WeirdConstructor/3DPrining_MakerGrid/res/containers.png

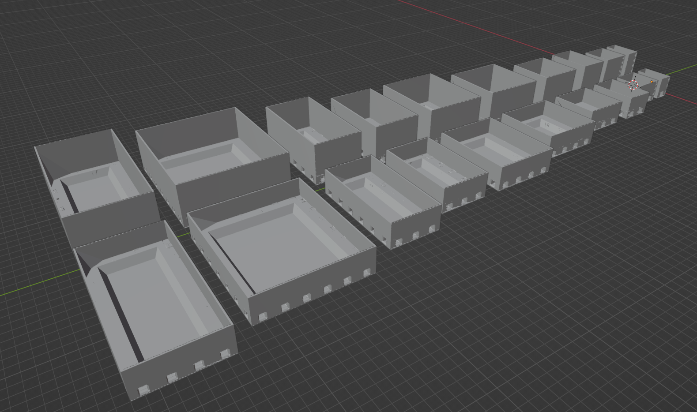
res/containers.png
