WeirdConstructor/3DPrining_MakerGrid/res/containers_demo.jpg

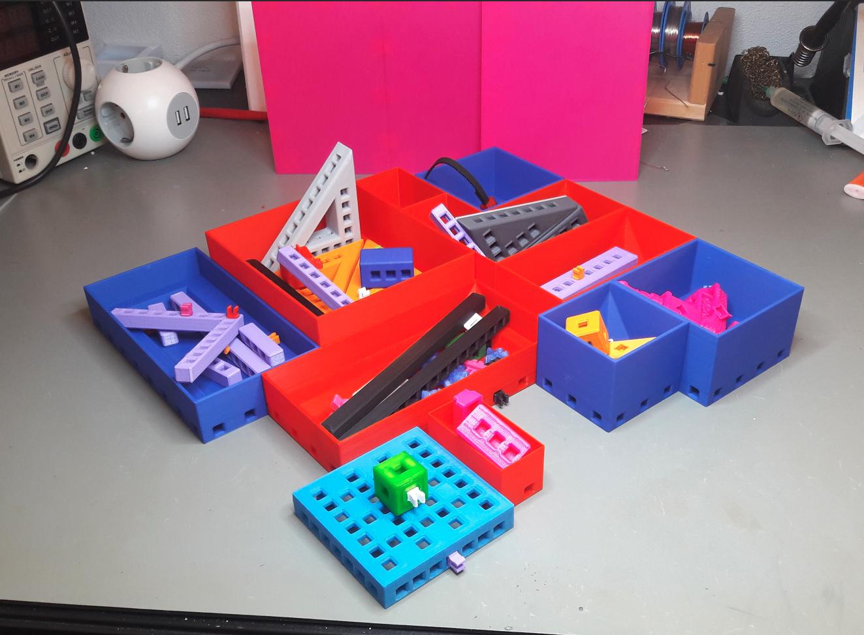
res/containers_demo.jpg
