WeirdConstructor/3DPrining_MakerGrid/res/fan_mount_50mm.jpg

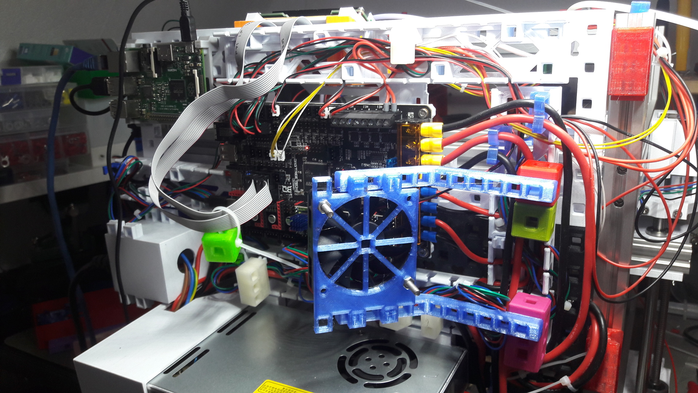
res/fan_mount_50mm.jpg
