WeirdConstructor/3DPrining_MakerGrid/res/fan_mount_120mm.jpg

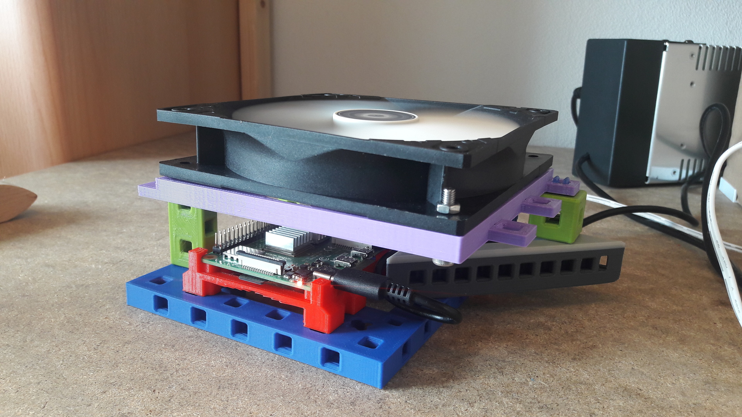
res/fan_mount_120mm.jpg
