WeirdConstructor/3DPrining_MakerGrid/res/m4_dovetail_mounts_demo.jpg

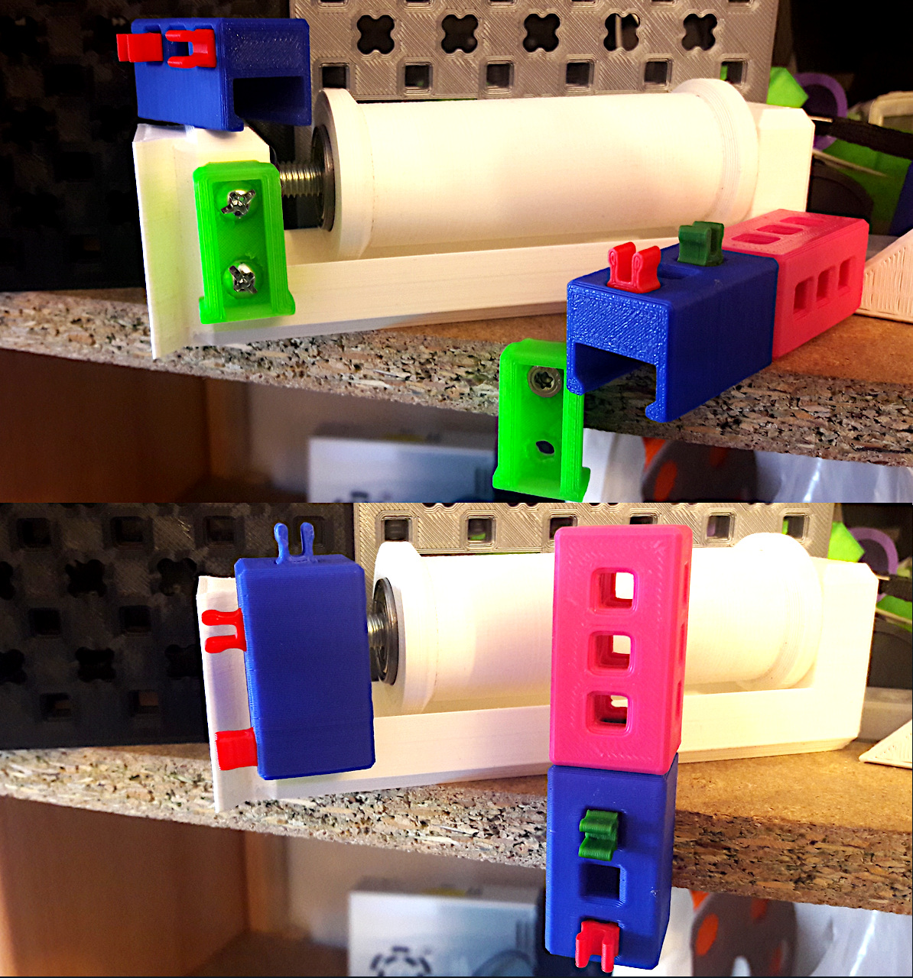
res/m4_dovetail_mounts_demo.jpg
