WeirdConstructor/3DPrining_MakerGrid/res/screwables_demo.jpg

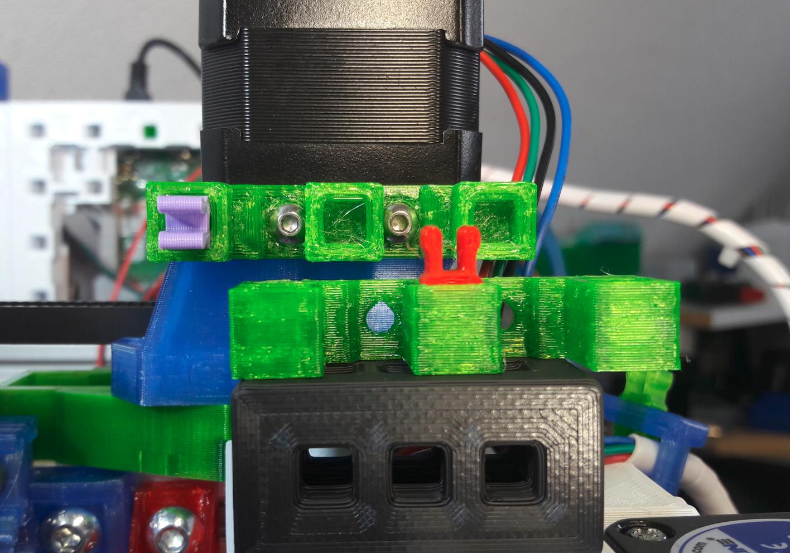
res/screwables_demo.jpg
