WeirdConstructor/3DPrining_MakerGrid/res/t_slot_20x20_nut6_mkg_clip_pic.jpg

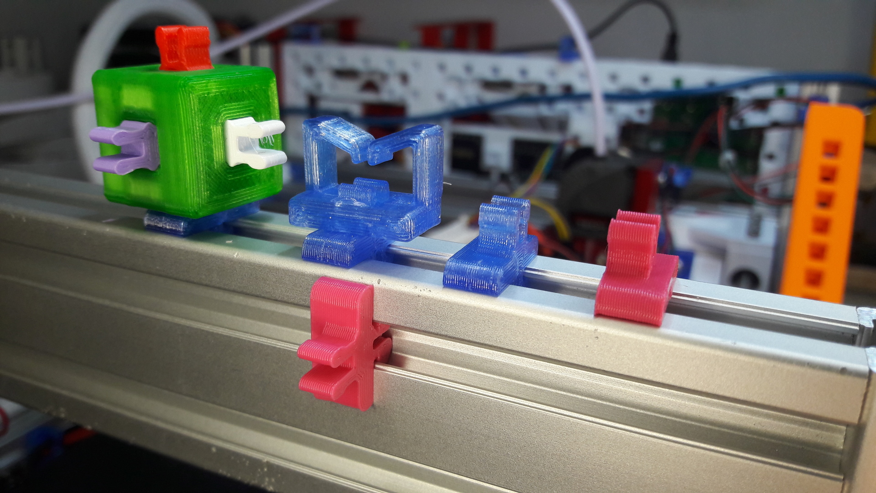
res/t_slot_20x20_nut6_mkg_clip_pic.jpg
