WeirdConstructor/3DPrining_MakerGrid/sliced/sliced_anycubic_i3_mega/clip_grid_2cm_type_b.3mf

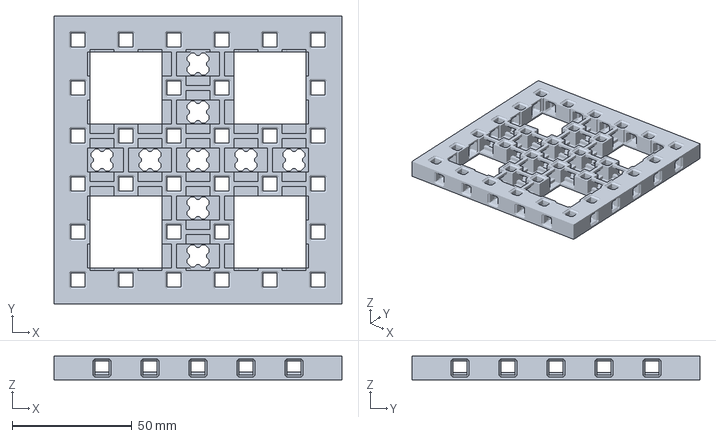
[picture p47: CAD file, 2022-01-15]
sliced/sliced_anycubic_i3_mega/clip_grid_2cm_type_b.3mf
120.0 x 120.0 x 10.0 mm
