WeirdConstructor/3DPrining_MakerGrid/sliced/sliced_kp3s/build_cubes-cube_side_con_11x1.3mf

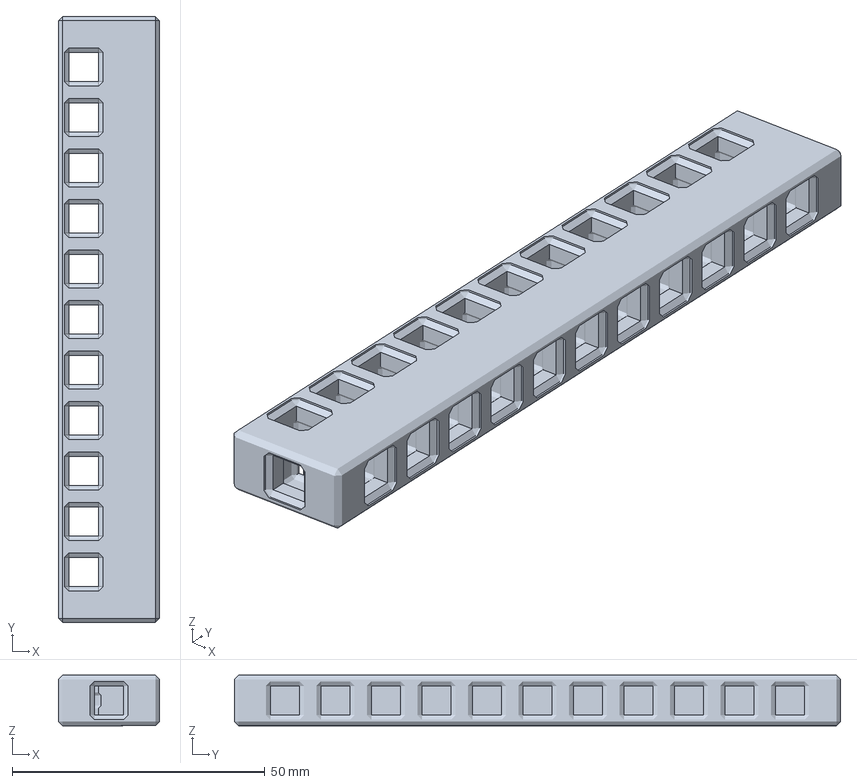
[picture p48: CAD file, 2022-01-27]
sliced/sliced_kp3s/build_cubes-cube_side_con_11x1.3mf
20.0 x 120.0 x 10.0 mm
