WeirdConstructor/3DPrining_MakerGrid/blender/cases/case_200x150x130-top_left.stl

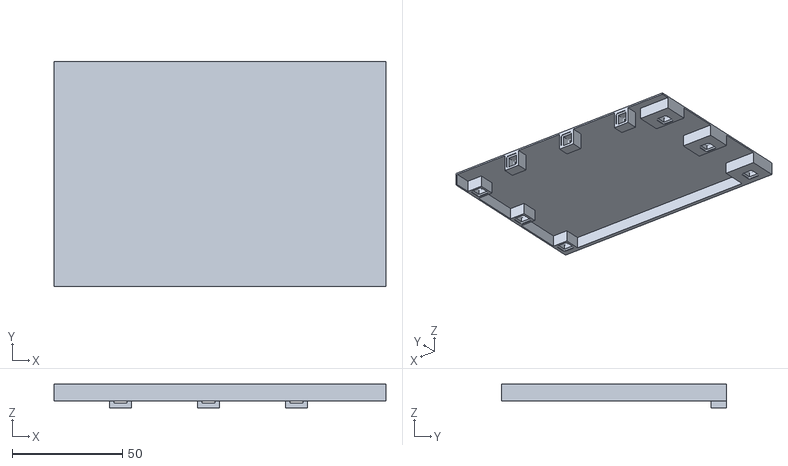
[picture p49: CAD file, 2024-06-11]
blender/cases/case_200x150x130-top_left.stl
150.9 x 102.4 x 10.7
