WeirdConstructor/3DPrining_MakerGrid/blender/clip_grid_2cm_case-cover_12x8.stl

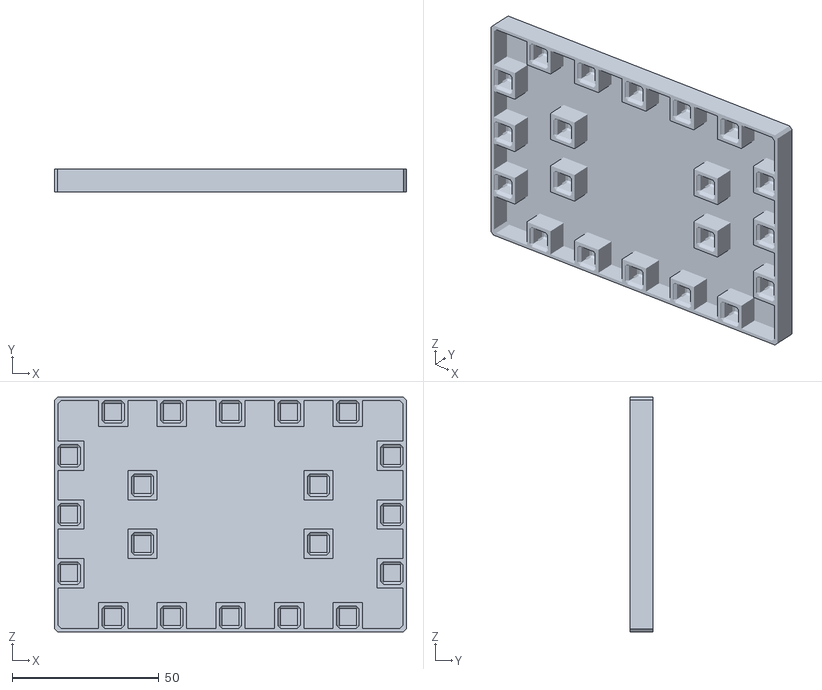
[picture p50: CAD file, 2024-04-21]
blender/clip_grid_2cm_case-cover_12x8.stl
120.0 x 7.89 x 80.0
