WeirdConstructor/3DPrining_MakerGrid/blender/devices/stepper_flag_Tight.stl

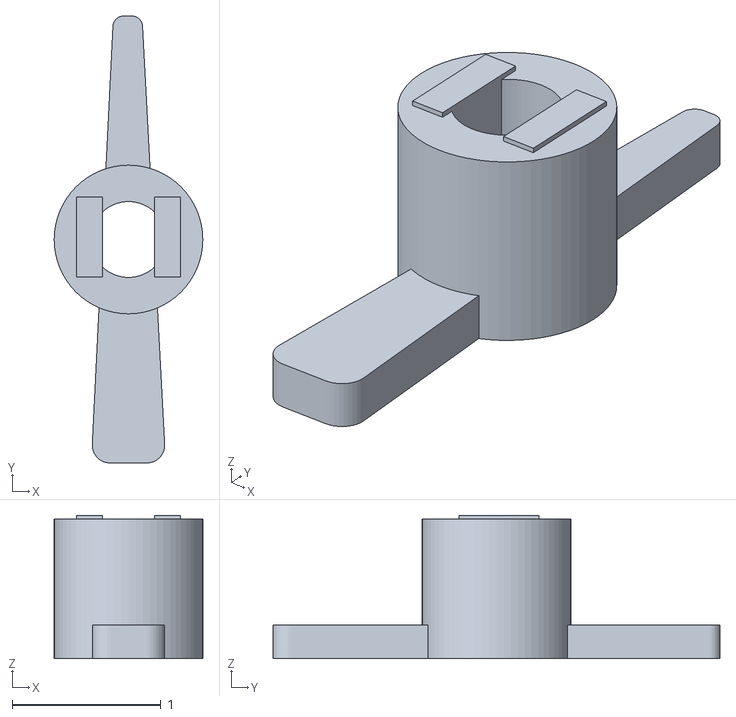
[picture p51: CAD file, 2024-04-28]
blender/devices/stepper_flag_Tight.stl
1.00 x 3.01 x 0.964
