WeirdConstructor/3DPrining_MakerGrid/blender/utils/hole_grid-hole_grid_pico.stl

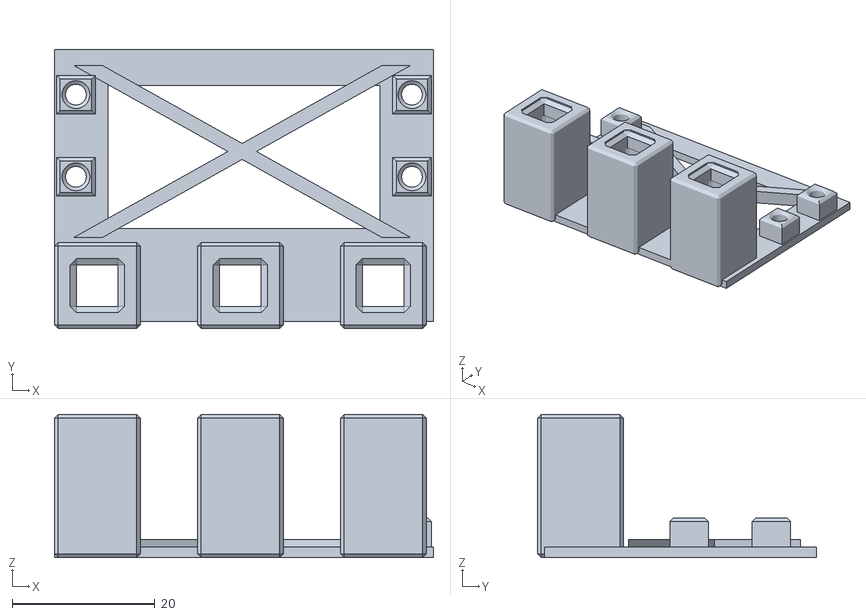
[picture p52: CAD file, 2024-06-11]
blender/utils/hole_grid-hole_grid_pico.stl
53.0 x 39.0 x 20.0
