WeirdConstructor/3DPrining_MakerGrid/sliced/sliced_anycubic_i3_mega/raspberry_pico_case_mkg_holder.3mf

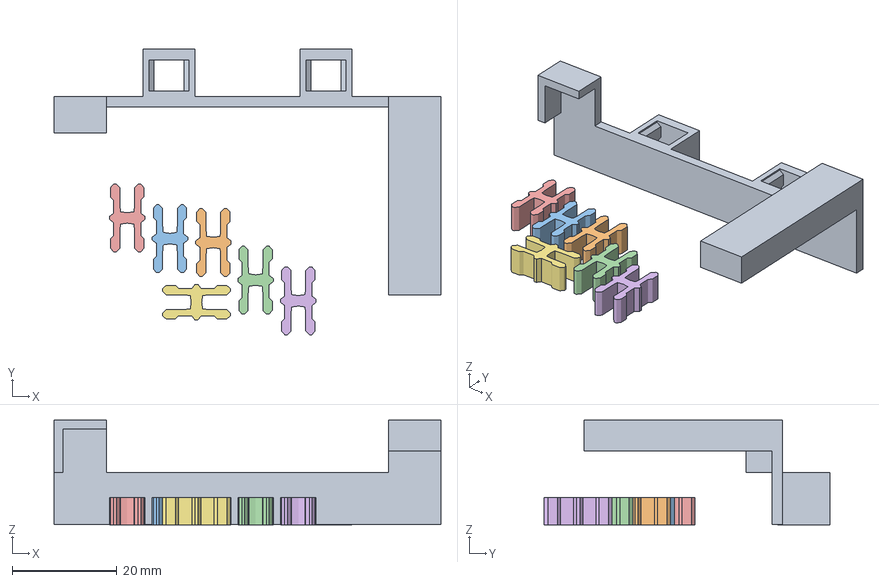
[picture p53: CAD file, 2022-01-14]
sliced/sliced_anycubic_i3_mega/raspberry_pico_case_mkg_holder.3mf
74.0 x 54.6 x 20.0 mm
raspberry_pico_case_mkg_holder.stl
clip.stl
clip.stl(1)
clip.stl(2)
clip.stl(3)
clip.stl(4)
clip.stl(5)
