WeirdConstructor/3DPrining_MakerGrid/sliced/sliced_kp3s/ptfe_tube-holder.3mf

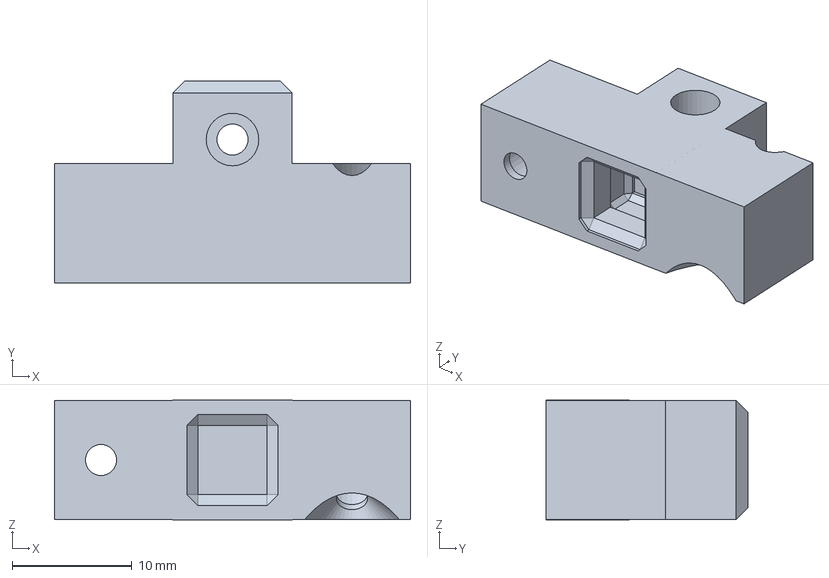
[picture p54: CAD file, 2022-01-24]
sliced/sliced_kp3s/ptfe_tube-holder.3mf
29.8 x 16.9 x 10.00 mm
