WeirdConstructor/3DPrining_MakerGrid/blender/Arduino-UNO.stl

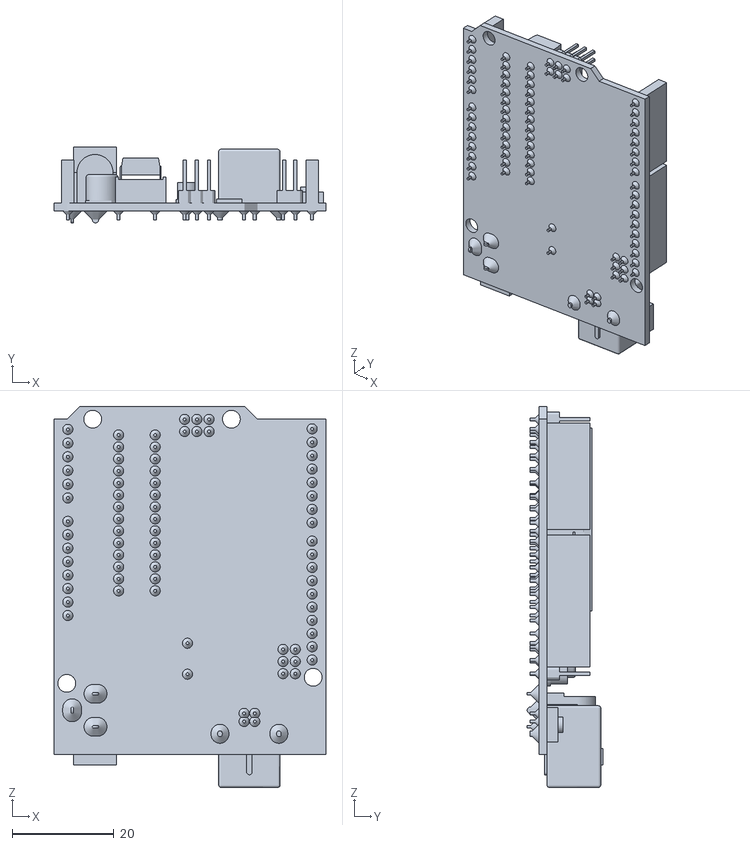
[picture p55: CAD file, 2024-03-30]
blender/Arduino-UNO.stl
53.5 x 14.9 x 75.0
