WeirdConstructor/3DPrining_MakerGrid/blender/devices/28byj-48_stepper_step_motor_holder-mkg_28byj_axis.stl

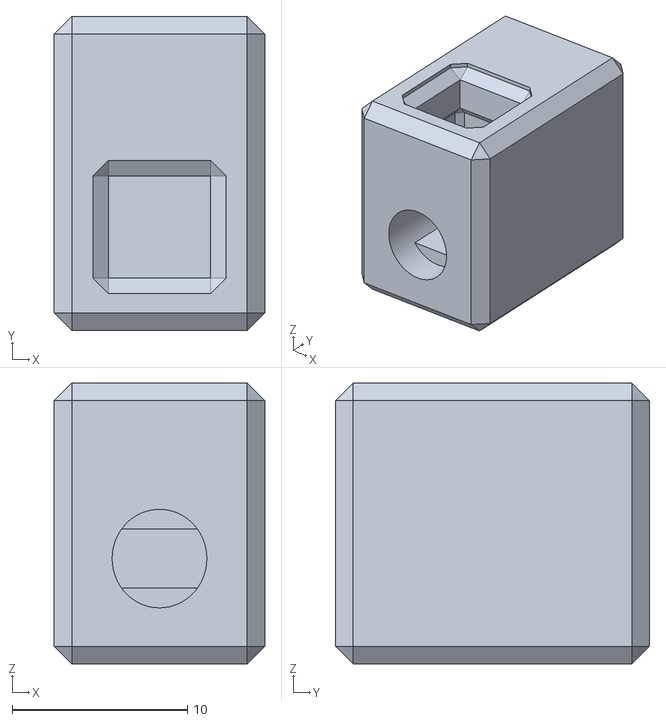
[picture p56: CAD file, 2024-04-28]
blender/devices/28byj-48_stepper_step_motor_holder-mkg_28byj_axis.stl
12.0 x 17.9 x 16.0
