WeirdConstructor/3DPrining_MakerGrid/blender/utils/plant_guide-hydro_wall_v2.stl

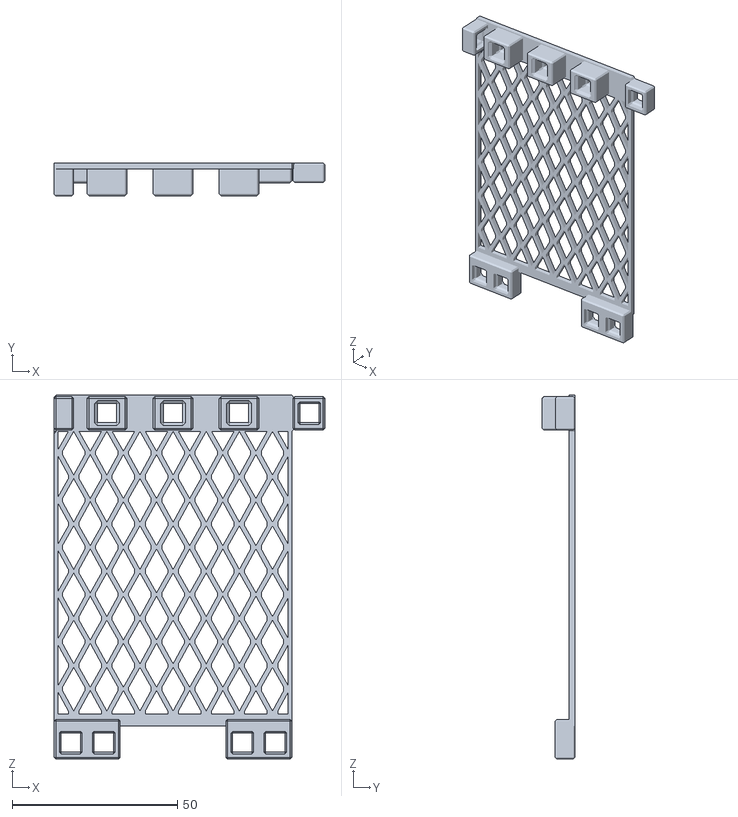
[picture p57: CAD file, 2024-06-11]
blender/utils/plant_guide-hydro_wall_v2.stl
82.0 x 10.0 x 110.3
