WeirdConstructor/3DPrining_MakerGrid/sliced/sliced_anycubic_i3_mega/cable_guide_a_v2.3mf

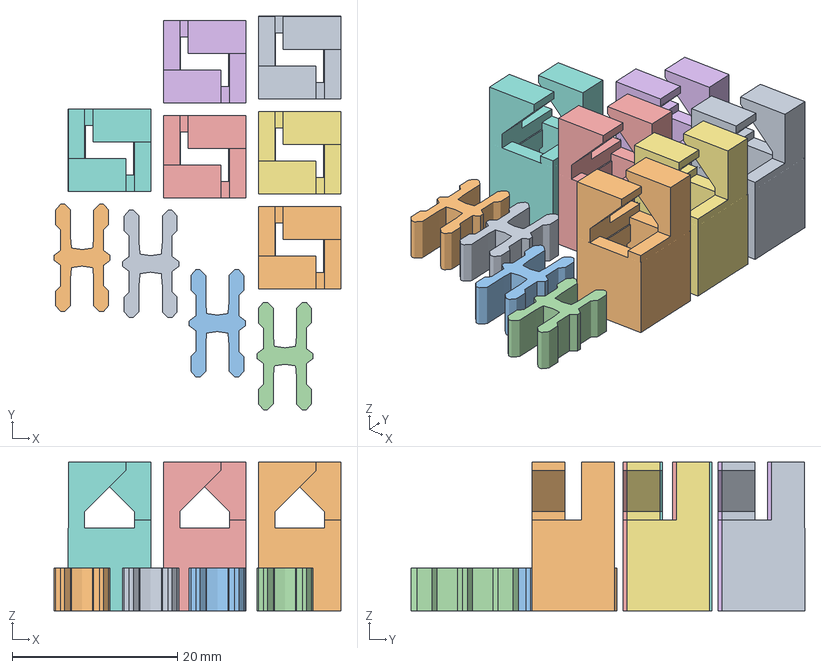
[picture p58: CAD file, 2022-01-14]
sliced/sliced_anycubic_i3_mega/cable_guide_a_v2.3mf
34.7 x 47.6 x 18.0 mm
clip.stl
clip.stl(1)
clip.stl(2)
clip.stl(4)
cable_guide_a_v2.stl
cable_guide_a_v2.stl(1)
cable_guide_a_v2.stl(2)
cable_guide_a_v2.stl(3)
cable_guide_a_v2.stl(4)
cable_guide_a_v2.stl(5)
