WeirdConstructor/3DPrining_MakerGrid/sliced/sliced_kp3s/glue_plate-plate_55x83.3mf

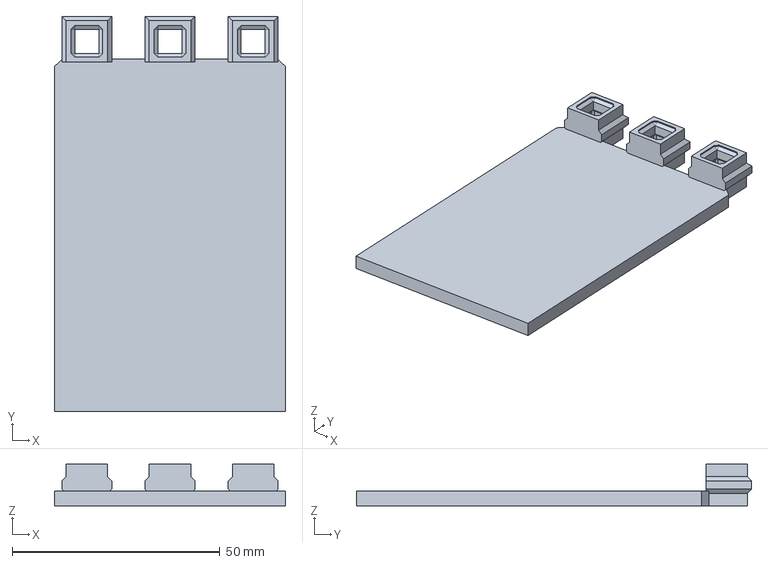
[picture p59: CAD file, 2022-01-24]
sliced/sliced_kp3s/glue_plate-plate_55x83.3mf
55.6 x 95.0 x 10.0 mm
