WeirdConstructor/3DPrining_MakerGrid/blender/cases/btt_octopus_plate-board_plate.stl

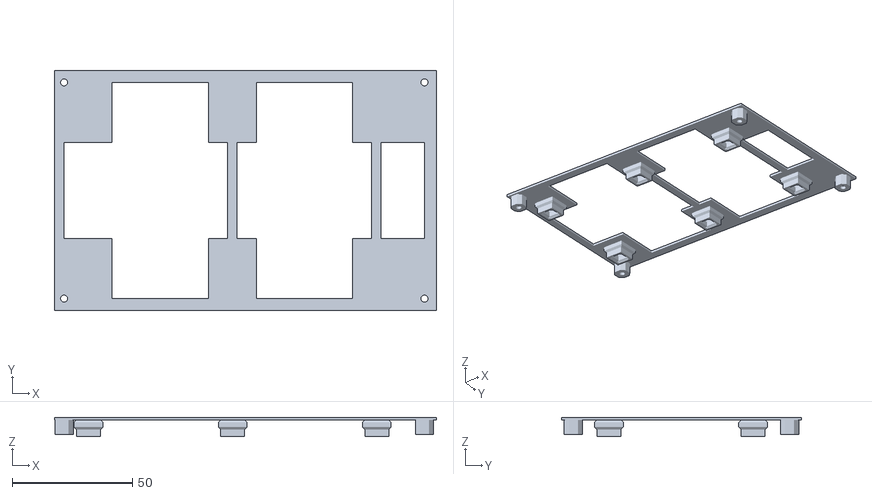
[picture p60: CAD file, 2022-03-17]
blender/cases/btt_octopus_plate-board_plate.stl
159.0 x 100.0 x 8.10
