WeirdConstructor/3DPrining_MakerGrid/blender/clip_grid_light_2cm-6x6.stl

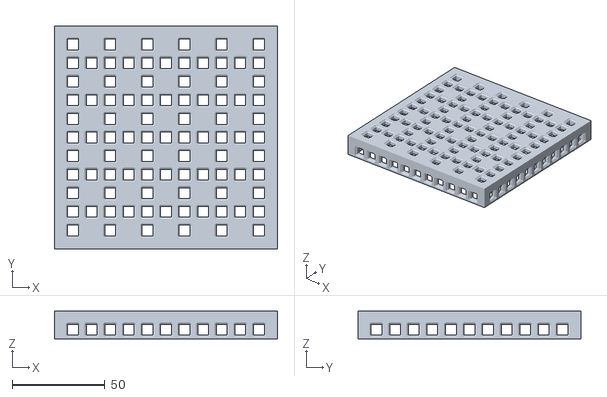
[picture p61: CAD file, 2022-06-01]
blender/clip_grid_light_2cm-6x6.stl
120.0 x 120.0 x 15.0
