WeirdConstructor/3DPrining_MakerGrid/blender/devices/Potentiometer.stl

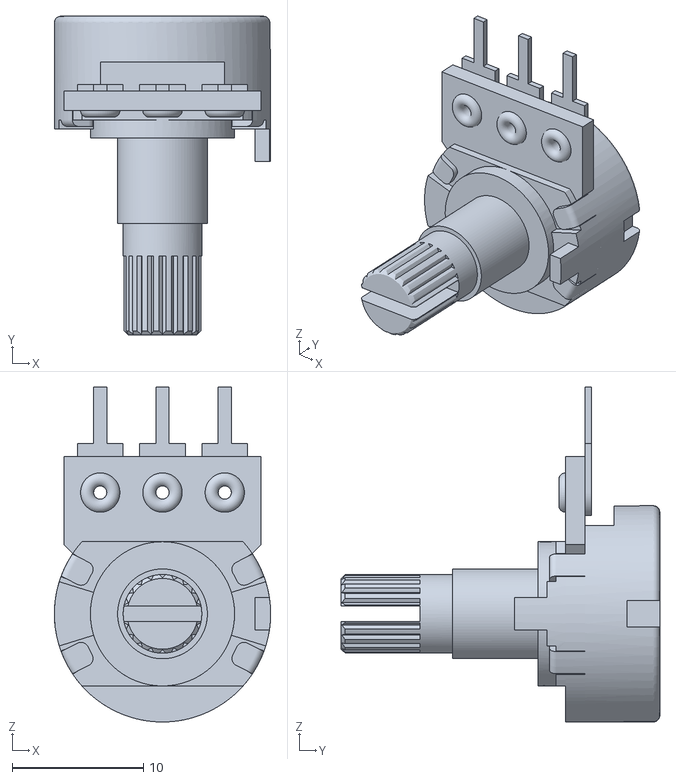
[picture p62: CAD file, 2024-04-28]
blender/devices/Potentiometer.stl
16.5 x 24.3 x 25.5
