WeirdConstructor/3DPrining_MakerGrid/blender/utils/hole_grid-gridcover_30x40.stl

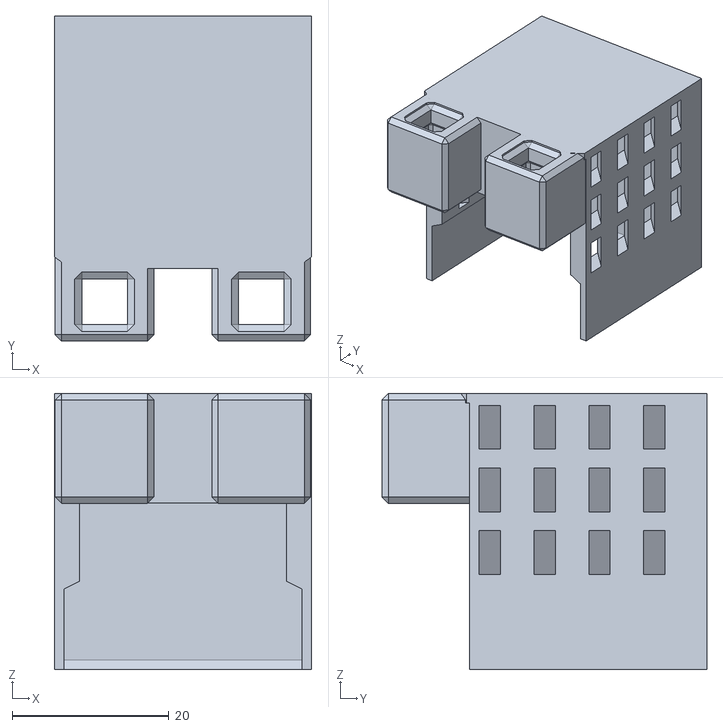
[picture p63: CAD file, 2024-06-11]
blender/utils/hole_grid-gridcover_30x40.stl
32.8 x 41.5 x 35.2
