WeirdConstructor/3DPrining_MakerGrid/sliced/sliced_kp3s/vise_holder-vise_4cm.3mf

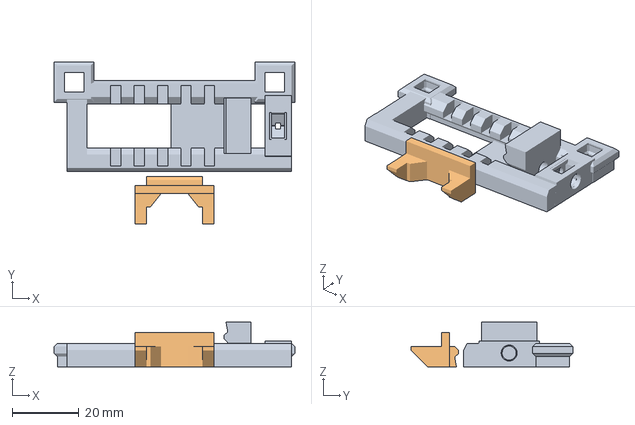
[picture p64: CAD file, 2022-01-20]
sliced/sliced_kp3s/vise_holder-vise_4cm.3mf
72.0 x 48.2 x 13.3 mm
vise_holder-vise_4cm.stl
vise_holder-vise_holder_insert.stl
