WeirdConstructor/3DPrining_MakerGrid/blender/cases/grid_case-wall_4x6.stl

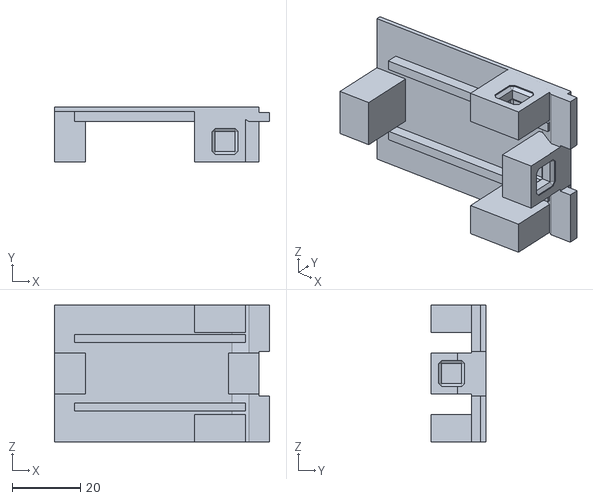
[picture p65: CAD file, 2022-02-05]
blender/cases/grid_case-wall_4x6.stl
62.9 x 16.0 x 40.0
