WeirdConstructor/3DPrining_MakerGrid/blender/clip_grid_light_2cm-2x2.stl

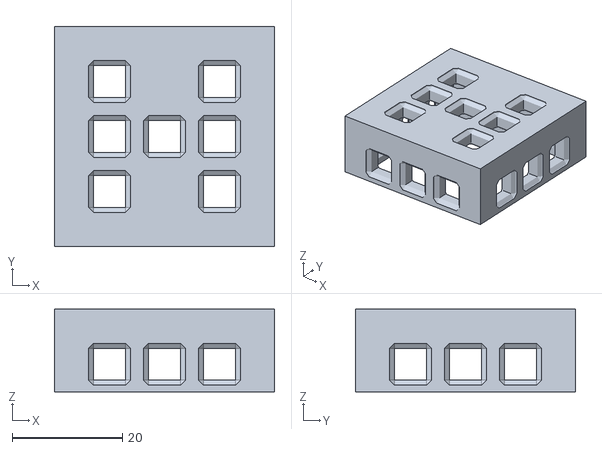
[picture p66: CAD file, 2022-06-01]
blender/clip_grid_light_2cm-2x2.stl
40.0 x 40.0 x 15.0
