WeirdConstructor/3DPrining_MakerGrid/blender/devices/servo_holder_40x20-block.stl

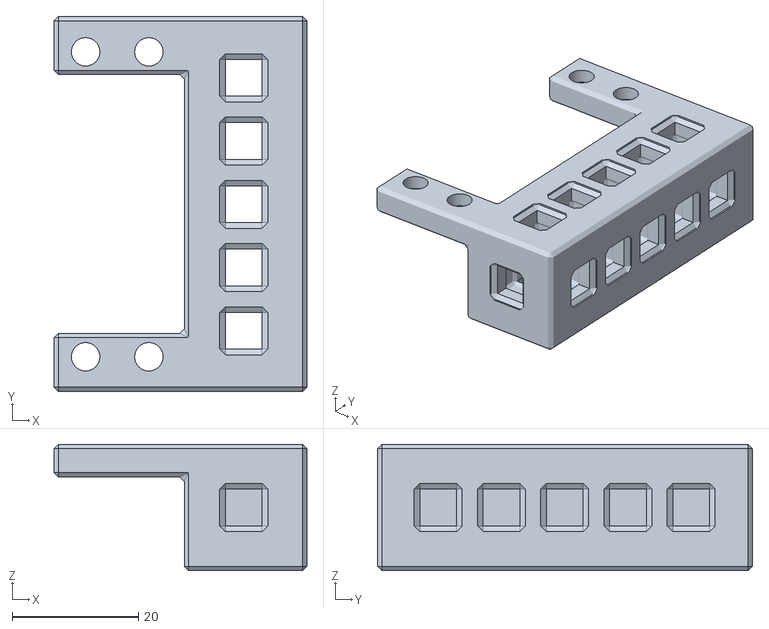
[picture p67: CAD file, 2024-04-28]
blender/devices/servo_holder_40x20-block.stl
40.0 x 59.3 x 20.0
