WeirdConstructor/3DPrining_MakerGrid/blender/utils/hole_grid-hole_grid_raspi.stl

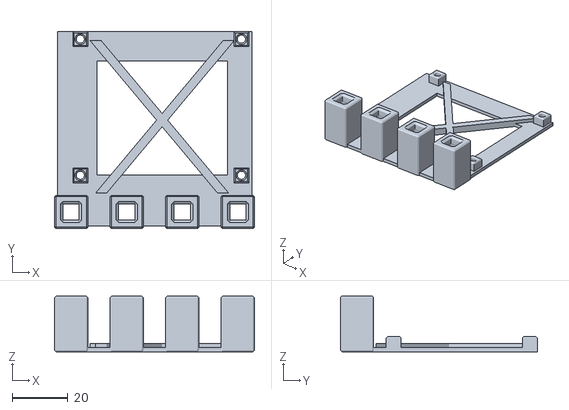
[picture p68: CAD file, 2024-06-11]
blender/utils/hole_grid-hole_grid_raspi.stl
72.0 x 71.0 x 20.0
