WeirdConstructor/3DPrining_MakerGrid/sliced/sliced_kp3s/angle_joints.3mf

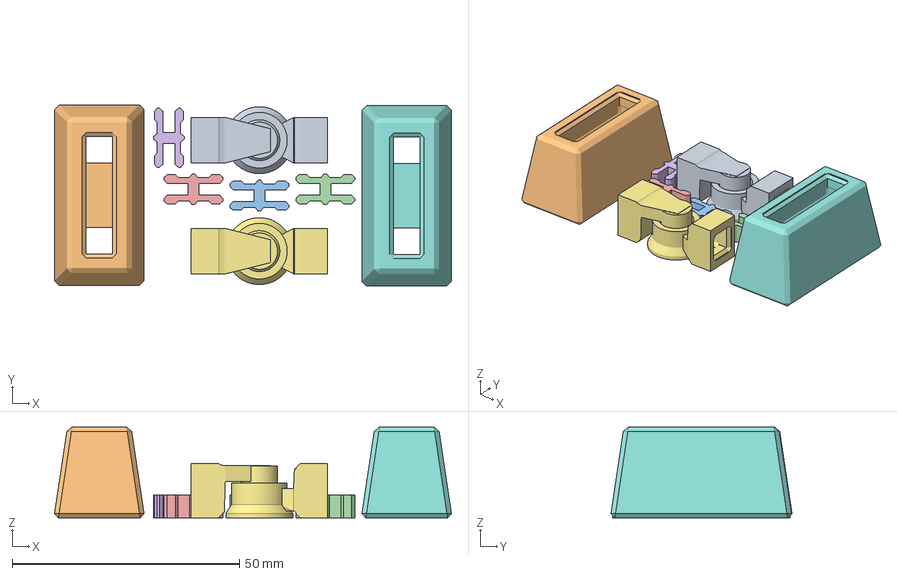
[picture p69: CAD file, 2022-01-18]
sliced/sliced_kp3s/angle_joints.3mf
87.3 x 39.8 x 20.0 mm
angle_joint-joint_type_a.stl
angle_joint-slide_block.stl
clip-clip.stl
clip-clip.stl(1)
clip-clip.stl(2)
clip-clip.stl(3)
angle_joint-joint_type_a.stl(1)
angle_joint-slide_block.stl(1)
