WeirdConstructor/3DPrining_MakerGrid/blender/cases/grid_case-side_4x12.stl

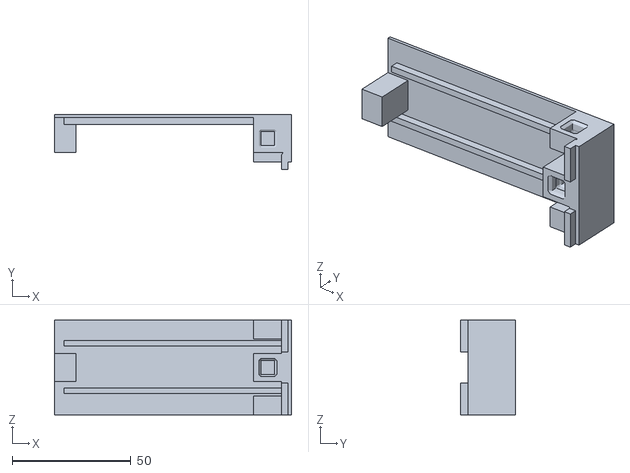
[picture p70: CAD file, 2022-02-04]
blender/cases/grid_case-side_4x12.stl
100.0 x 23.0 x 40.0
