WeirdConstructor/3DPrining_MakerGrid/blender/clip_grid_light_2cm-3x3.stl

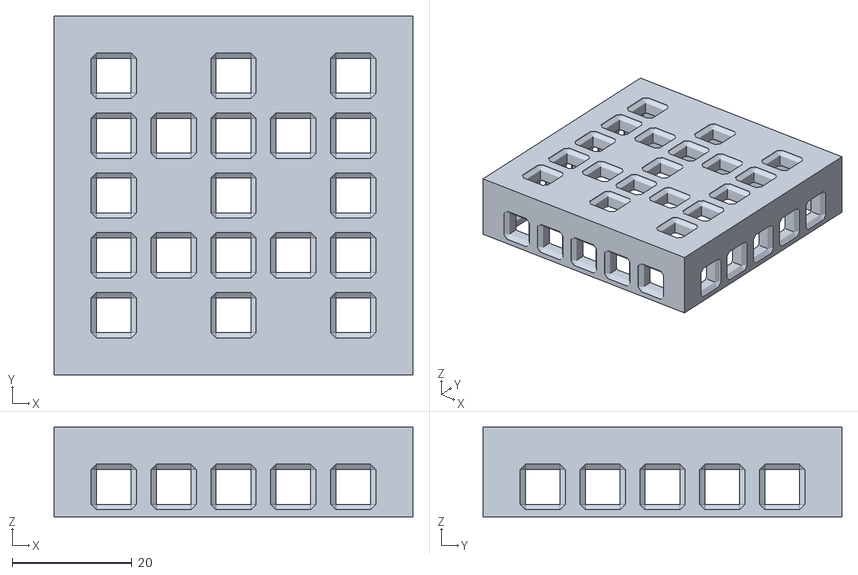
[picture p71: CAD file, 2022-06-01]
blender/clip_grid_light_2cm-3x3.stl
60.0 x 60.0 x 15.0
