WeirdConstructor/3DPrining_MakerGrid/blender/devices/elgato_hold_dovetail-elgato_hold_sides.stl

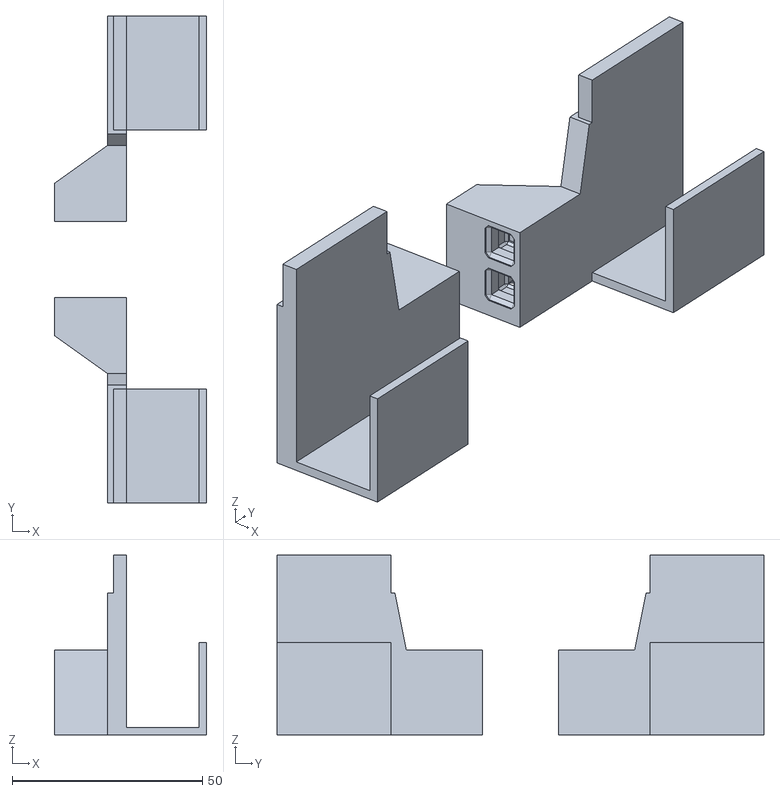
[picture p72: CAD file, 2024-04-28]
blender/devices/elgato_hold_dovetail-elgato_hold_sides.stl
40.0 x 128.0 x 47.3
