WeirdConstructor/3DPrining_MakerGrid/blender/utils/hole_grid-14x16mm_perfb.stl

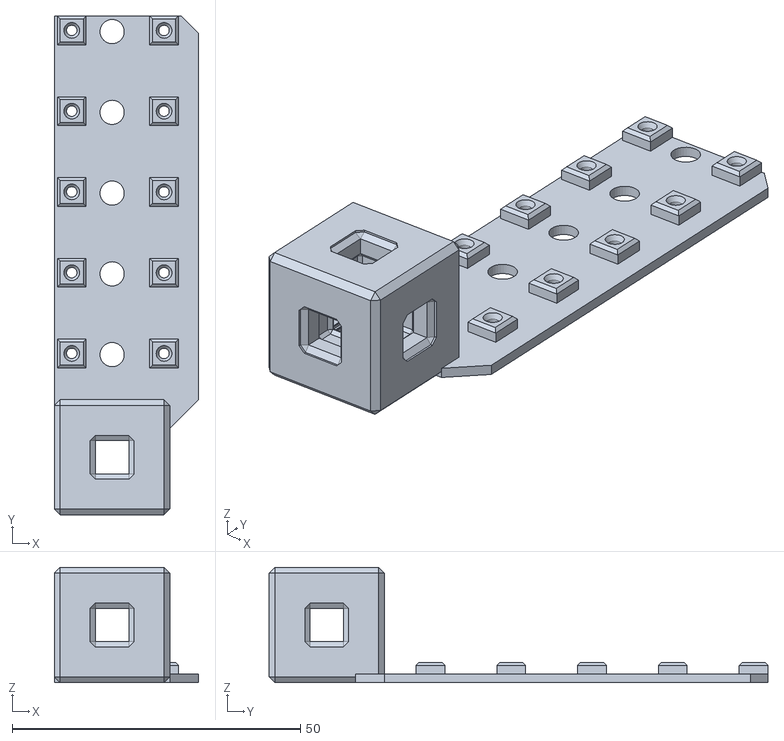
[picture p73: CAD file, 2024-06-11]
blender/utils/hole_grid-14x16mm_perfb.stl
25.0 x 86.5 x 20.0
