WeirdConstructor/3DPrining_MakerGrid/sliced/sliced_kp3s/build_cubes-cubes_x.3mf

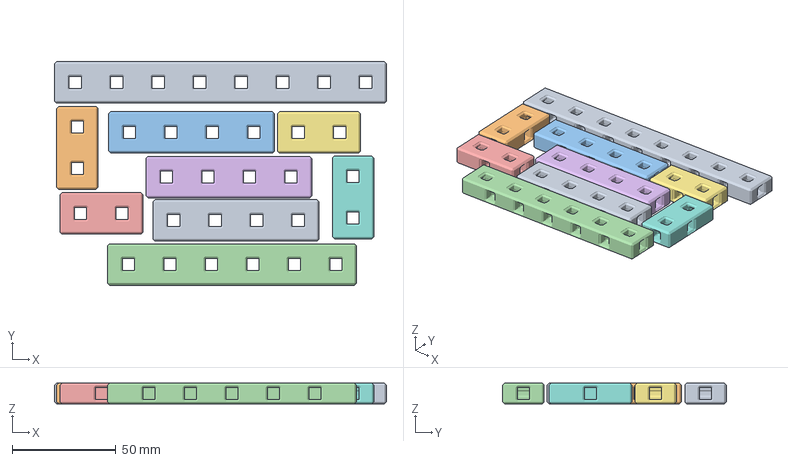
[picture p74: CAD file, 2022-01-18]
sliced/sliced_kp3s/build_cubes-cubes_x.3mf
160.0 x 107.8 x 10.0 mm
build_cubes-cube_15x1_x.stl
build_cubes-cube_3x1_x.stl
build_cubes-cube_7x1_x.stl
build_cubes-cube_11x1_x.stl
build_cubes-cube_3x1_x.stl(1)
build_cubes-cube_7x1_x.stl(1)
build_cubes-cube_3x1_x.stl(2)
build_cubes-cube_3x1_x.stl(3)
build_cubes-cube_7x1_x.stl(2)
