WeirdConstructor/3DPrining_MakerGrid/blender/clip_grid_light_2cm-4x4.stl

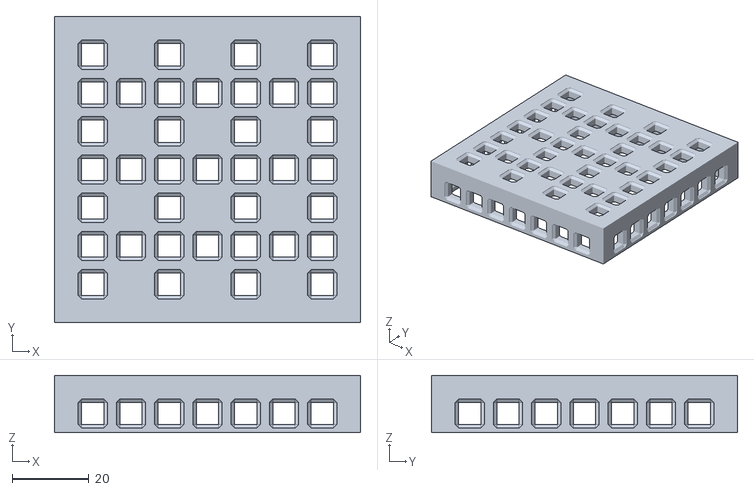
[picture p76: CAD file, 2022-06-01]
blender/clip_grid_light_2cm-4x4.stl
80.0 x 80.0 x 15.0
