WeirdConstructor/3DPrining_MakerGrid/blender/devices/28byj-48_stepper_step_motor_holder-mkg_poti_clip.stl

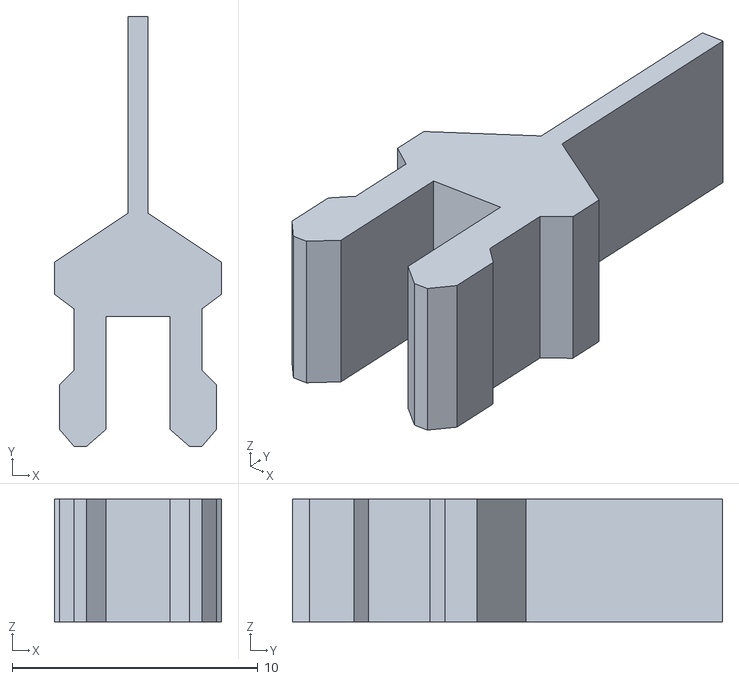
[picture p77: CAD file, 2024-04-28]
blender/devices/28byj-48_stepper_step_motor_holder-mkg_poti_clip.stl
6.80 x 17.5 x 5.00
