WeirdConstructor/3DPrining_MakerGrid/blender/utils/plant_guide-19cm_pot_clamp.stl

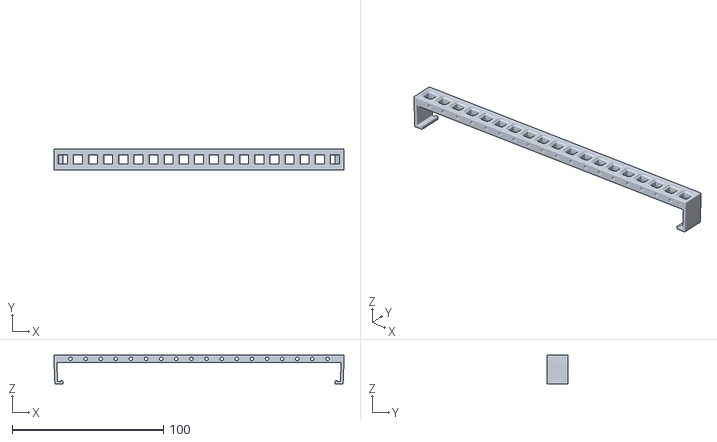
[picture p78: CAD file, 2024-06-11]
blender/utils/plant_guide-19cm_pot_clamp.stl
191.8 x 14.0 x 19.0
