WeirdConstructor/3DPrining_MakerGrid/sliced/sliced_kp3s/clip-mini_clip.3mf

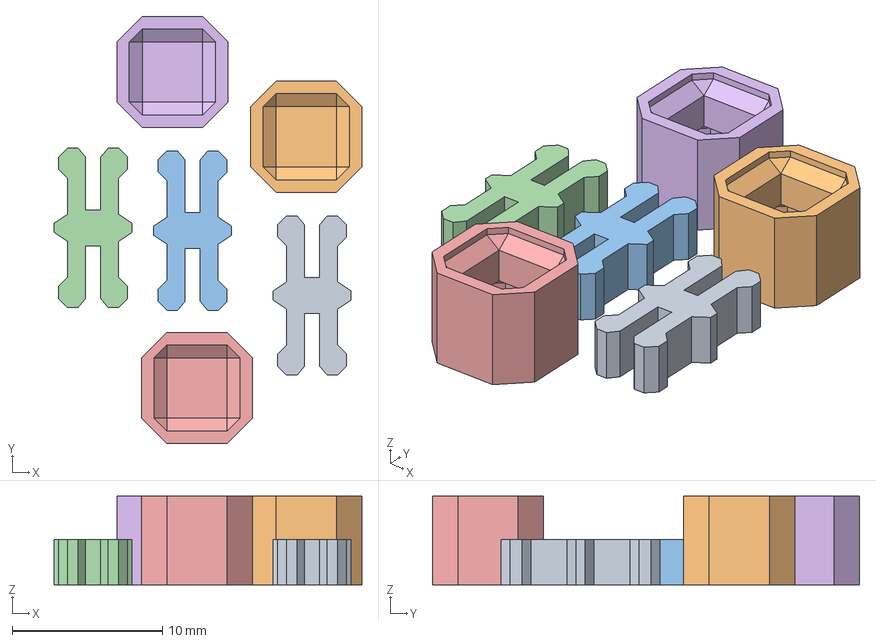
[picture p79: CAD file, 2022-01-18]
sliced/sliced_kp3s/clip-mini_clip.3mf
20.5 x 28.4 x 5.90 mm
clip-mini_clip.stl
clip-mini_clip_holder.stl
clip-mini_clip.stl(1)
clip-mini_clip.stl(2)
clip-mini_clip_holder.stl(1)
clip-mini_clip_holder.stl(2)
