WeirdConstructor/3DPrining_MakerGrid/blender/cases/grid_case-12x12_top_grid.stl

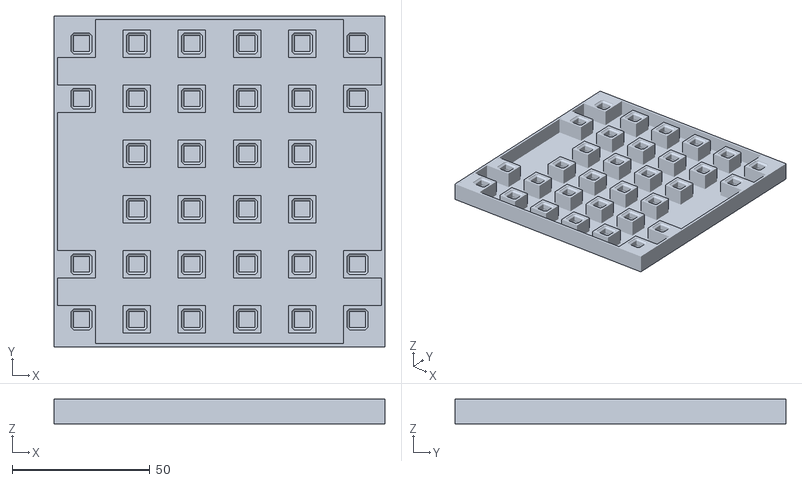
[picture p80: CAD file, 2022-02-02]
blender/cases/grid_case-12x12_top_grid.stl
120.0 x 120.0 x 9.00
