WeirdConstructor/3DPrining_MakerGrid/blender/clip_grid_light_2cm-5x5.stl

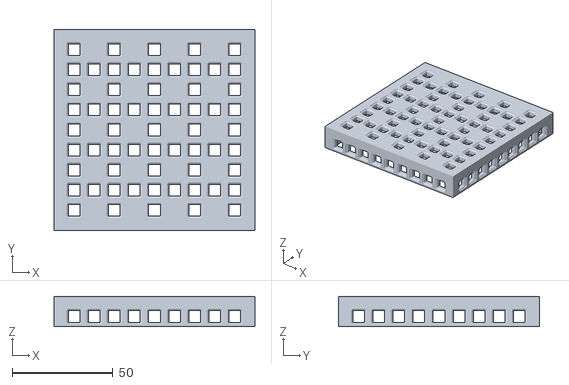
[picture p81: CAD file, 2022-06-01]
blender/clip_grid_light_2cm-5x5.stl
100.0 x 100.0 x 15.0
