WeirdConstructor/3DPrining_MakerGrid/blender/devices/servo_holder_40x20-mkg_servo_horn_addon.stl

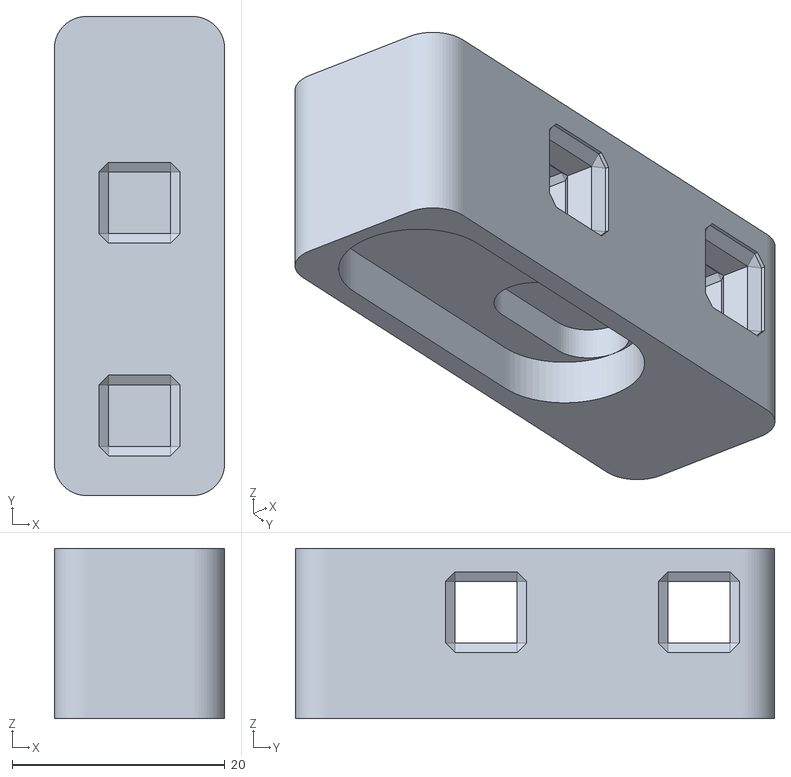
[picture p82: CAD file, 2024-04-28]
blender/devices/servo_holder_40x20-mkg_servo_horn_addon.stl
16.0 x 45.0 x 16.0
