WeirdConstructor/3DPrining_MakerGrid/blender/utils/hole_grid-hole_grid_10x30.stl

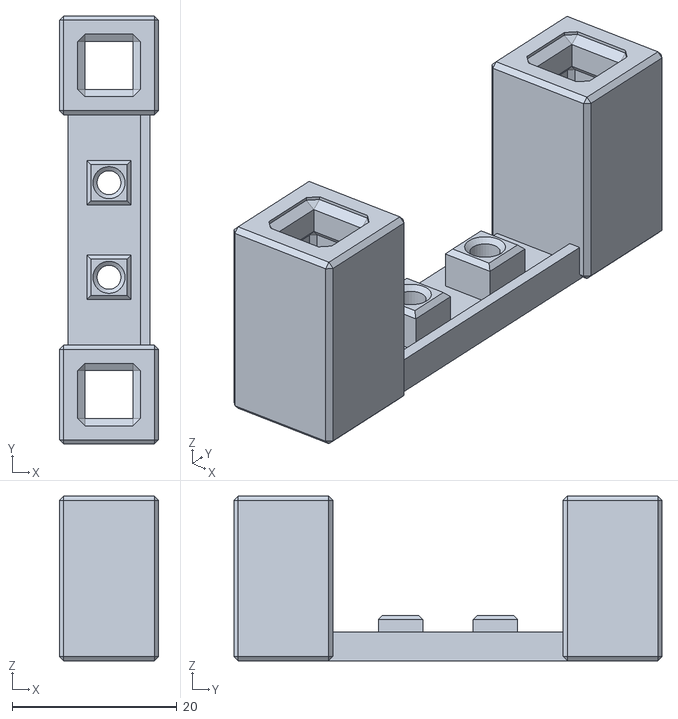
[picture p83: CAD file, 2024-06-11]
blender/utils/hole_grid-hole_grid_10x30.stl
12.0 x 52.0 x 20.0
