WeirdConstructor/3DPrining_MakerGrid/sliced/sliced_kp3s/cube_1x1_3x1_7x1_clips.3mf

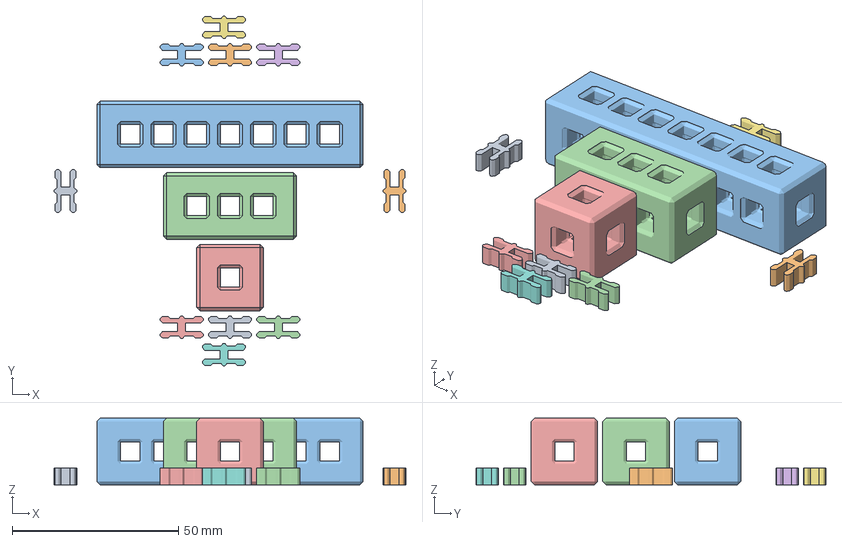
[picture p84: CAD file, 2022-01-18]
sliced/sliced_kp3s/cube_1x1_3x1_7x1_clips.3mf
105.6 x 105.1 x 20.0 mm
clip-clip.stl
clip-clip.stl(1)
clip-clip.stl(2)
clip-clip.stl(3)
clip-clip.stl(4)
clip-clip.stl(5)
clip-clip.stl(6)
clip-clip.stl(7)
clip-clip.stl(8)
clip-clip.stl(9)
build_cubes-cube_7x1.stl
build_cubes-cube_3x1.stl
build_cubes-cube_1x1.stl
