WeirdConstructor/3DPrining_MakerGrid/blender/cases/grid_case-side_8x12.stl

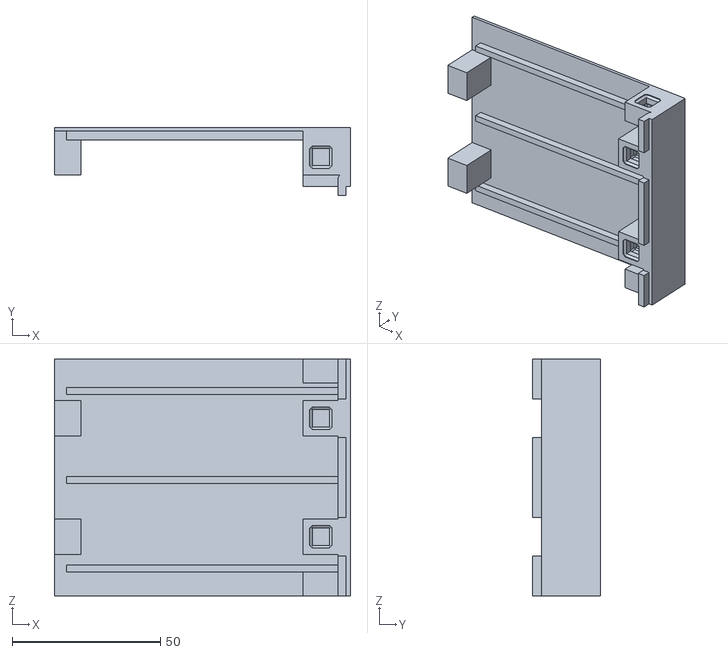
[picture p85: CAD file, 2022-02-02]
blender/cases/grid_case-side_8x12.stl
100.0 x 23.0 x 80.0
