WeirdConstructor/3DPrining_MakerGrid/blender/mak_a_blok-MakABlok_offset.stl

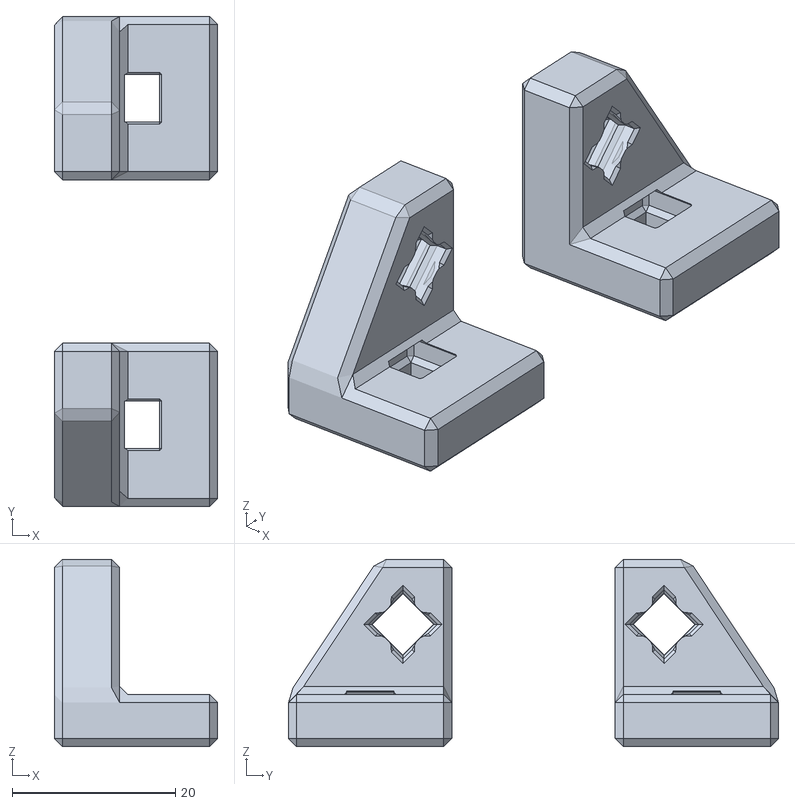
[picture p86: CAD file, 2022-05-27]
blender/mak_a_blok-MakABlok_offset.stl
20.0 x 60.0 x 23.0
