WeirdConstructor/3DPrining_MakerGrid/blender/utils/plant_guide-door_hinge.stl

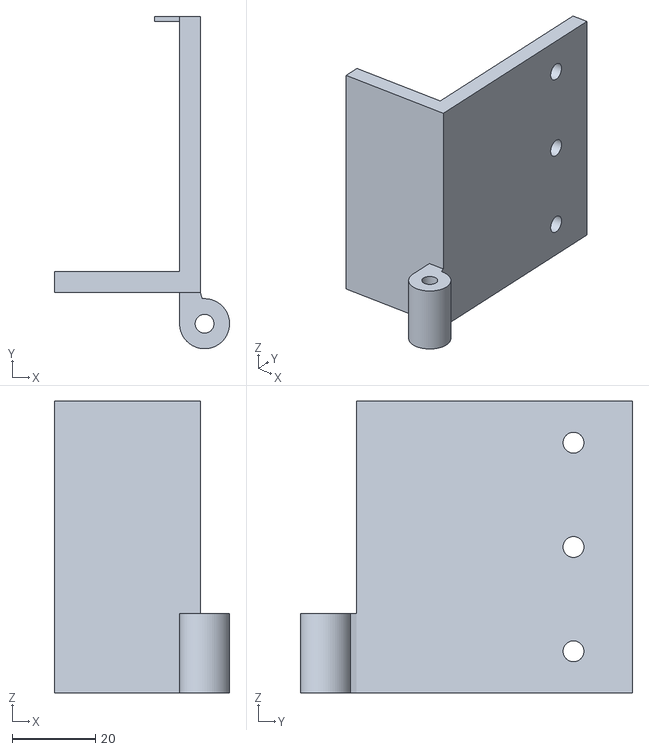
[picture p87: CAD file, 2024-06-11]
blender/utils/plant_guide-door_hinge.stl
42.0 x 79.7 x 70.0
