WeirdConstructor/3DPrining_MakerGrid/sliced/sliced_kp3s/raspberry_pi_plate-holder.3mf

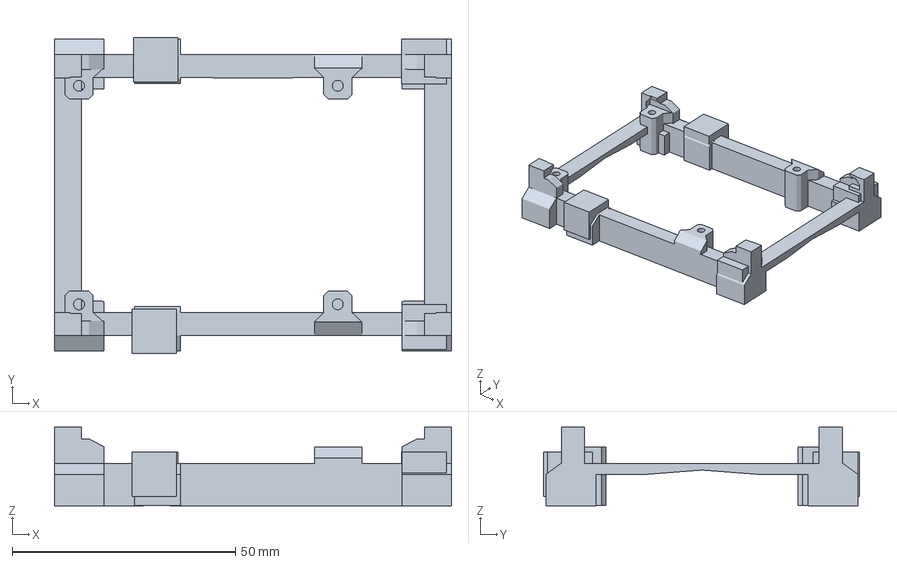
[picture p88: CAD file, 2022-01-18]
sliced/sliced_kp3s/raspberry_pi_plate-holder.3mf
89.0 x 70.9 x 17.6 mm
