WeirdConstructor/3DPrining_MakerGrid/blender/cases/grid_case-wall_8x6.stl

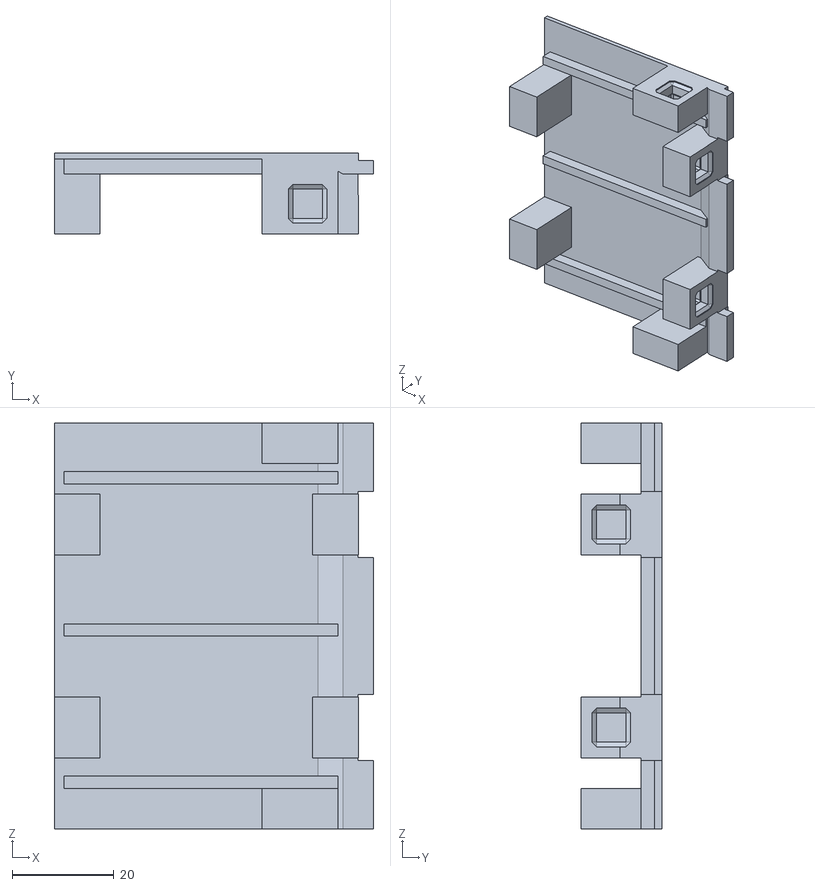
[picture p89: CAD file, 2022-02-02]
blender/cases/grid_case-wall_8x6.stl
62.9 x 16.0 x 80.0
