WeirdConstructor/3DPrining_MakerGrid/blender/devices/elgato_hold_dovetail-elgato_hold_top.stl

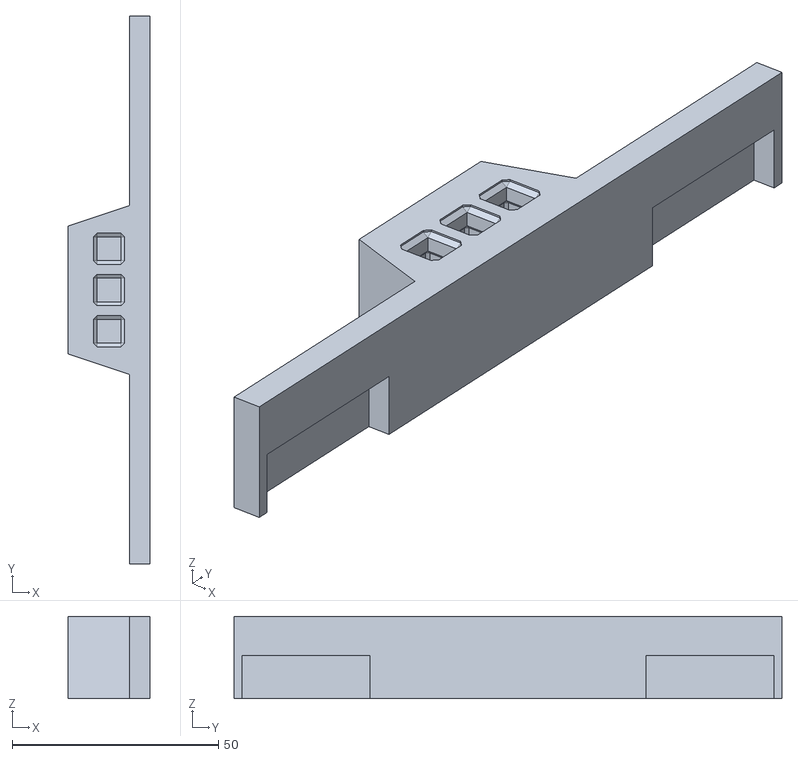
[picture p90: CAD file, 2024-04-28]
blender/devices/elgato_hold_dovetail-elgato_hold_top.stl
20.0 x 133.0 x 20.0
