WeirdConstructor/3DPrining_MakerGrid/blender/utils/plant_guide-backplate.stl

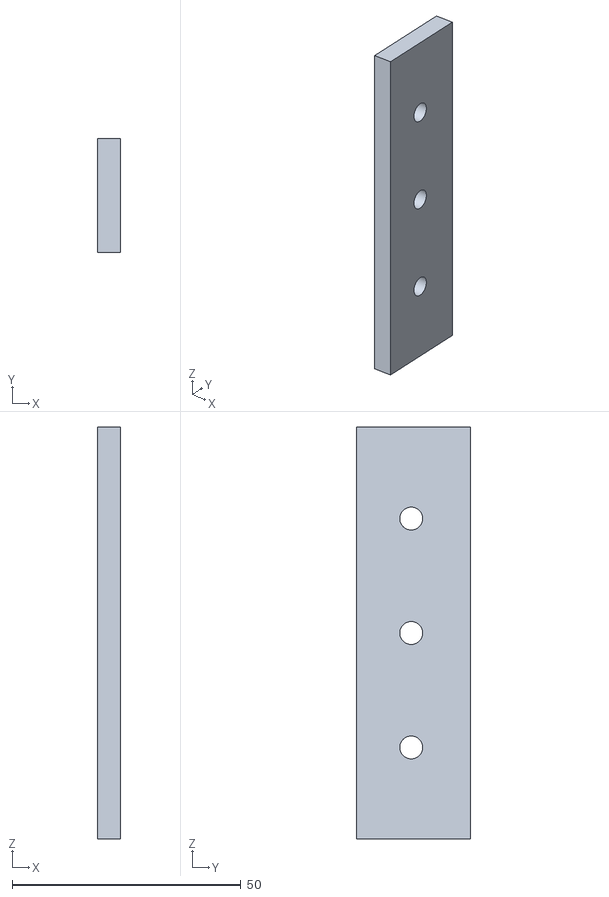
[picture p92: CAD file, 2024-06-11]
blender/utils/plant_guide-backplate.stl
5.00 x 25.0 x 90.0
