WeirdConstructor/3DPrining_MakerGrid/blender/cases/grid_case-12x12_6mm_height.stl

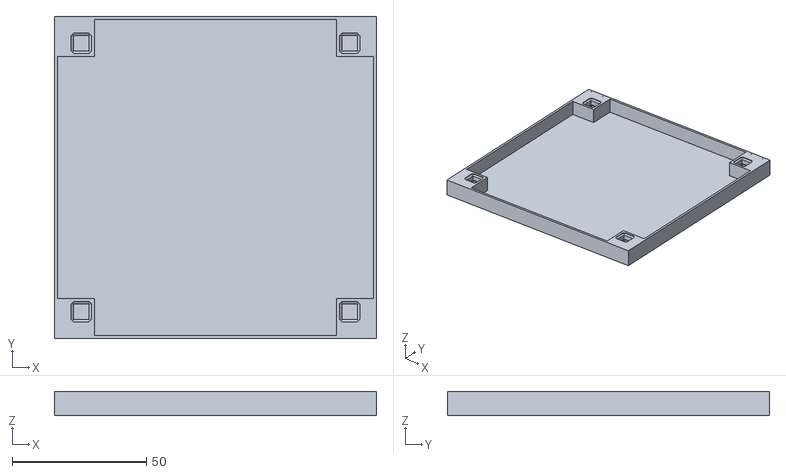
[picture p94: CAD file, 2022-02-01]
blender/cases/grid_case-12x12_6mm_height.stl
120.0 x 120.0 x 9.00
