WeirdConstructor/3DPrining_MakerGrid/blender/devices/28byj-48_stepper_step_motor_holder-pot_mount.stl

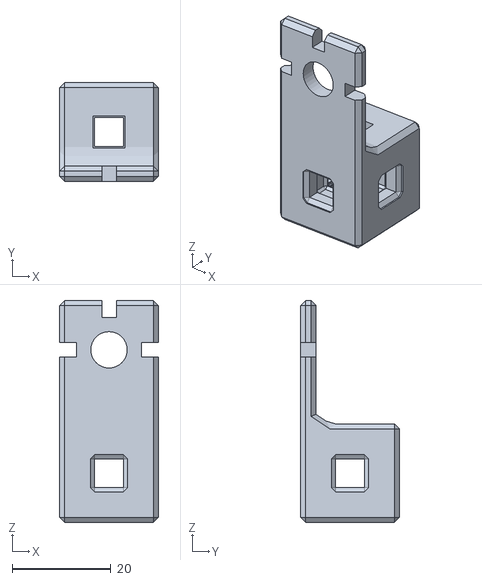
[picture p95: CAD file, 2024-04-28]
blender/devices/28byj-48_stepper_step_motor_holder-pot_mount.stl
20.0 x 20.0 x 45.0
