WeirdConstructor/3DPrining_MakerGrid/blender/mak_a_blok-MakABlok_cube.stl

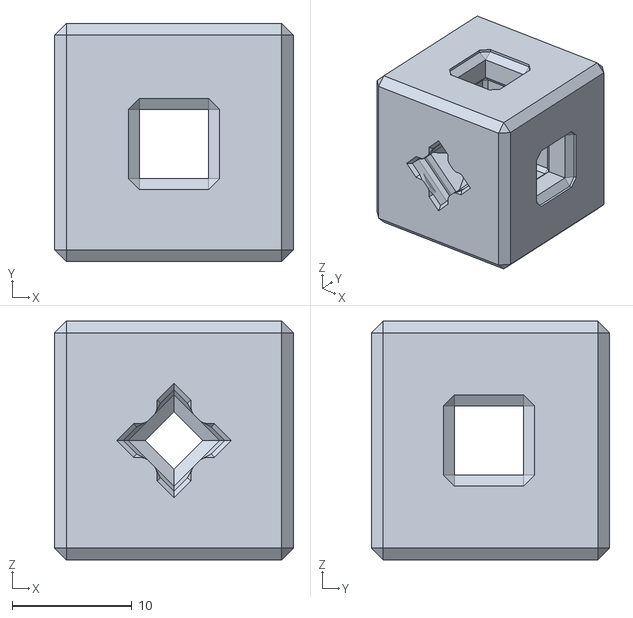
[picture p96: CAD file, 2022-05-27]
blender/mak_a_blok-MakABlok_cube.stl
20.0 x 20.0 x 20.0
