WeirdConstructor/3DPrining_MakerGrid/blender/utils/plant_guide-hydro_wall.stl

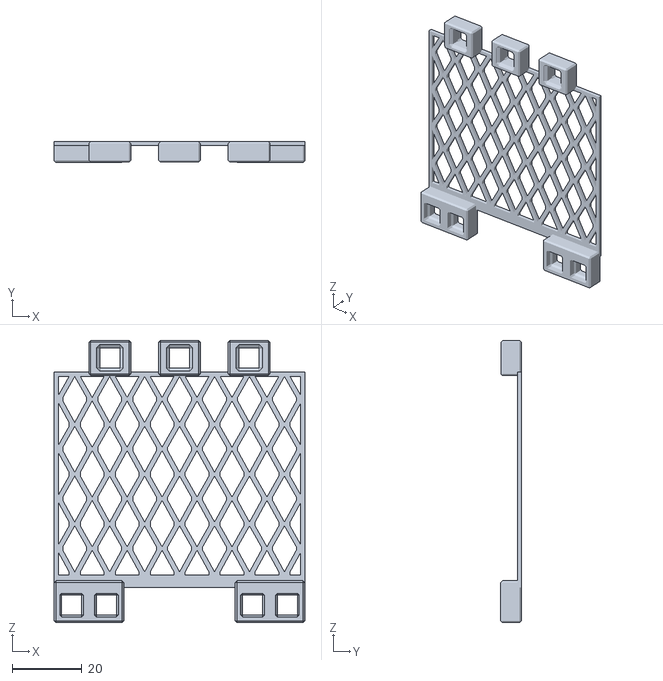
[picture p97: CAD file, 2024-06-11]
blender/utils/plant_guide-hydro_wall.stl
72.0 x 6.00 x 81.0
