WeirdConstructor/3DPrining_MakerGrid/blender/devices/ptfe_holds-maker_grid_pfte_9mm_thread_hold.stl

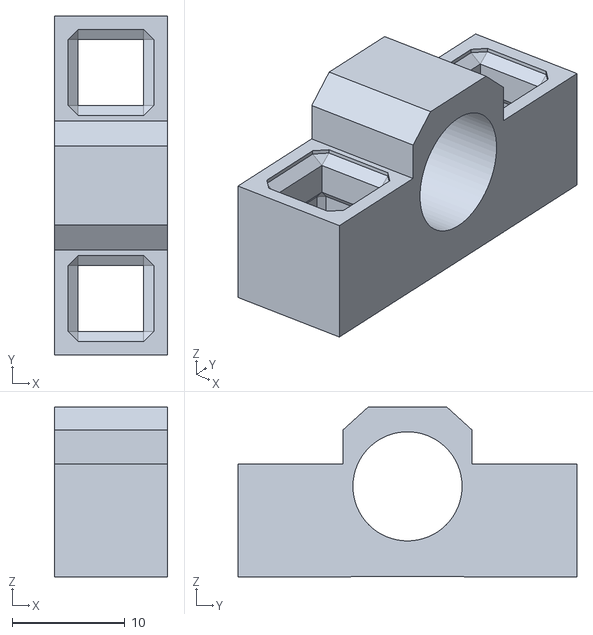
[picture p98: CAD file, 2022-06-09]
blender/devices/ptfe_holds-maker_grid_pfte_9mm_thread_hold.stl
10.0 x 30.0 x 15.0
