WeirdConstructor/3DPrining_MakerGrid/blender/mak_a_blok-MakABlok_blok.stl

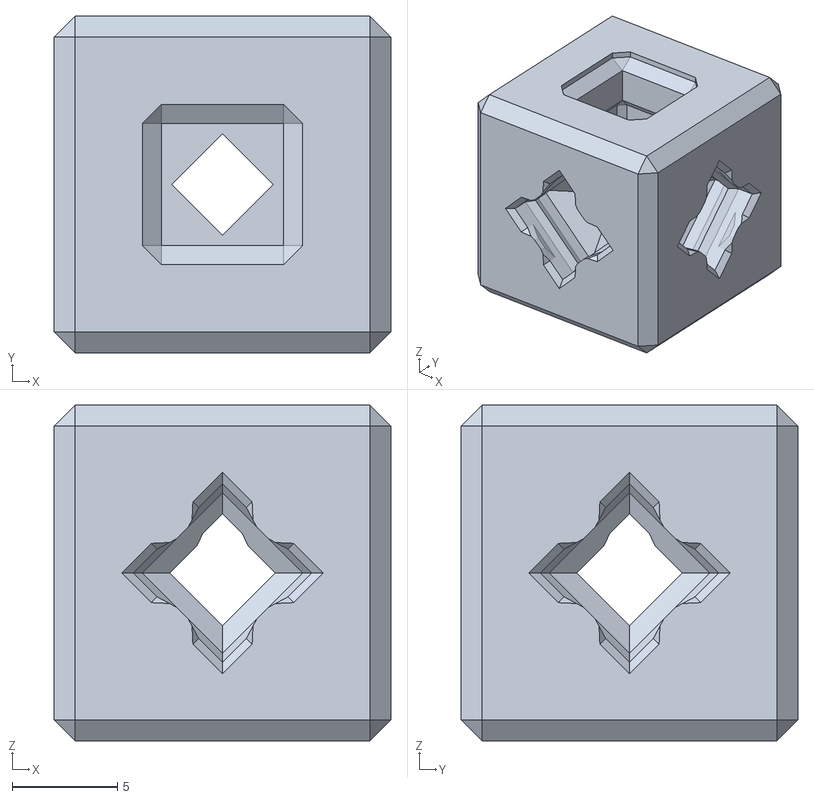
[picture p99: CAD file, 2022-05-26]
blender/mak_a_blok-MakABlok_blok.stl
16.0 x 16.0 x 15.9
