WeirdConstructor/3DPrining_MakerGrid/blender/utils/plant_guide-styroclamp_LH.stl

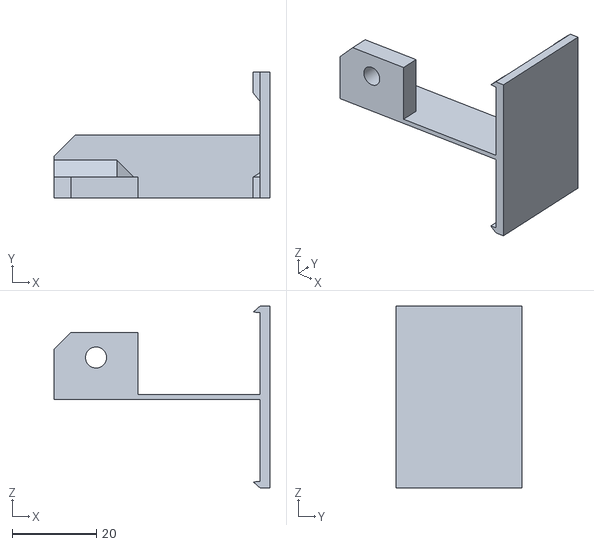
[picture p100: CAD file, 2024-06-11]
blender/utils/plant_guide-styroclamp_LH.stl
51.4 x 30.0 x 43.2
