WeirdConstructor/3DPrining_MakerGrid/blender/cases/vise_holder_large-vise_4cm.stl

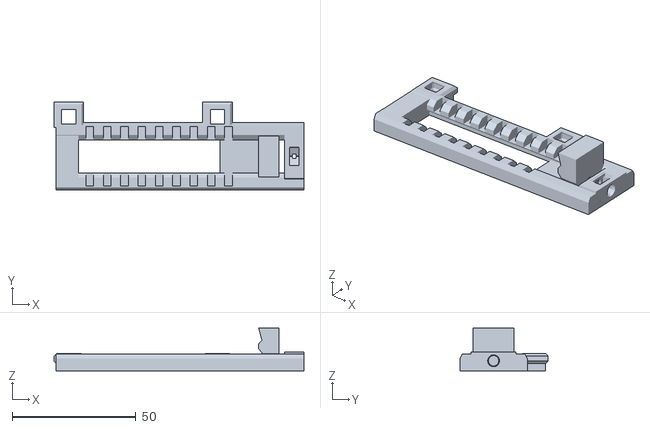
[picture p102: CAD file, 2022-01-22]
blender/cases/vise_holder_large-vise_4cm.stl
100.9 x 35.6 x 17.3
