WeirdConstructor/3DPrining_MakerGrid/blender/devices/led_strip_case-cover.stl

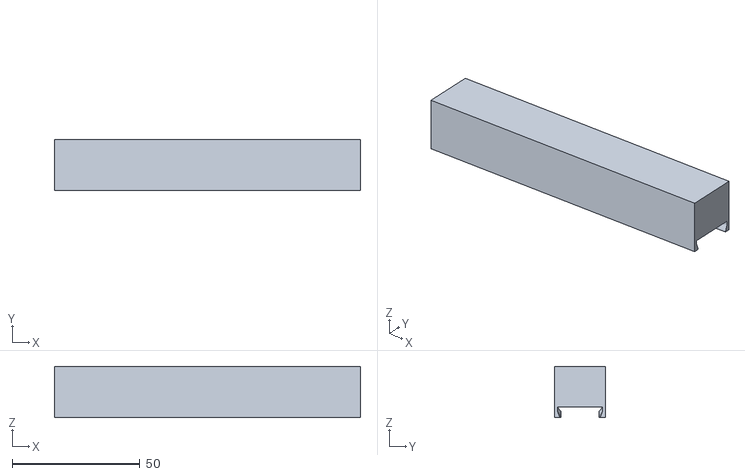
[picture p103: CAD file, 2022-01-31]
blender/devices/led_strip_case-cover.stl
120.0 x 20.0 x 20.1
