WeirdConstructor/3DPrining_MakerGrid/blender/mak_a_blok-MakABlok_clip_connector.stl

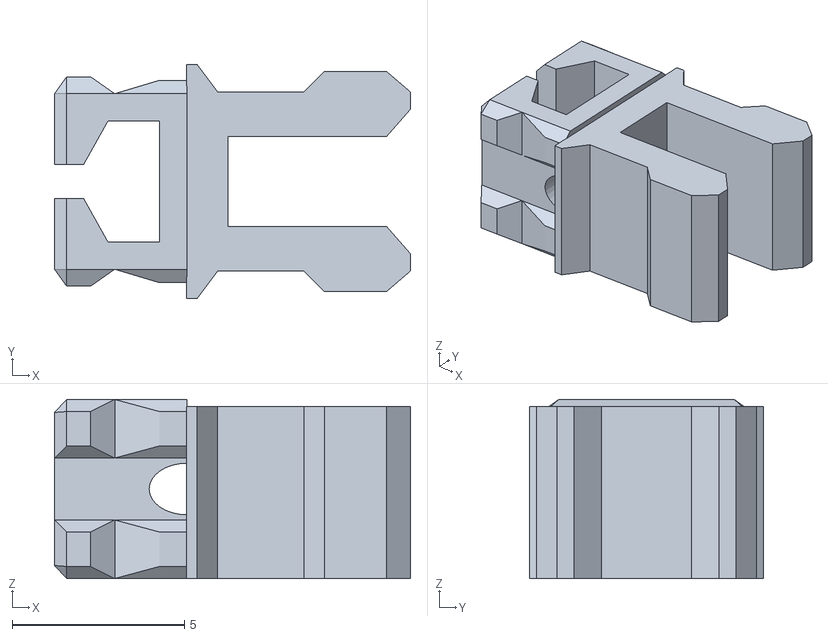
[picture p104: CAD file, 2022-05-26]
blender/mak_a_blok-MakABlok_clip_connector.stl
10.3 x 6.80 x 5.20
