WeirdConstructor/3DPrining_MakerGrid/sliced/sliced_kp3s/clip_grid_2cm.3mf

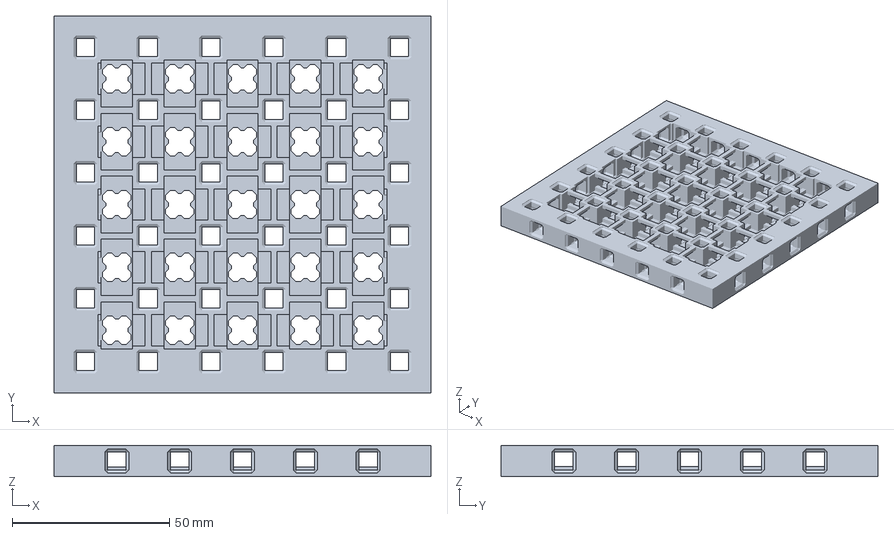
[picture p106: CAD file, 2022-01-15]
sliced/sliced_kp3s/clip_grid_2cm.3mf
120.0 x 120.0 x 10.00 mm
