WeirdConstructor/3DPrining_MakerGrid/blender/cases/vise_holder_large-vise_holder_insert.stl

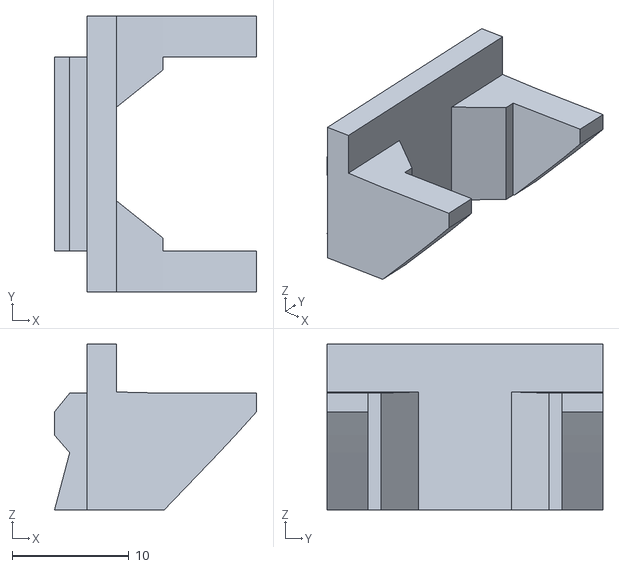
[picture p107: CAD file, 2022-01-22]
blender/cases/vise_holder_large-vise_holder_insert.stl
17.3 x 23.6 x 14.2
