WeirdConstructor/3DPrining_MakerGrid/blender/clip-clip_hole_cad_export.stl

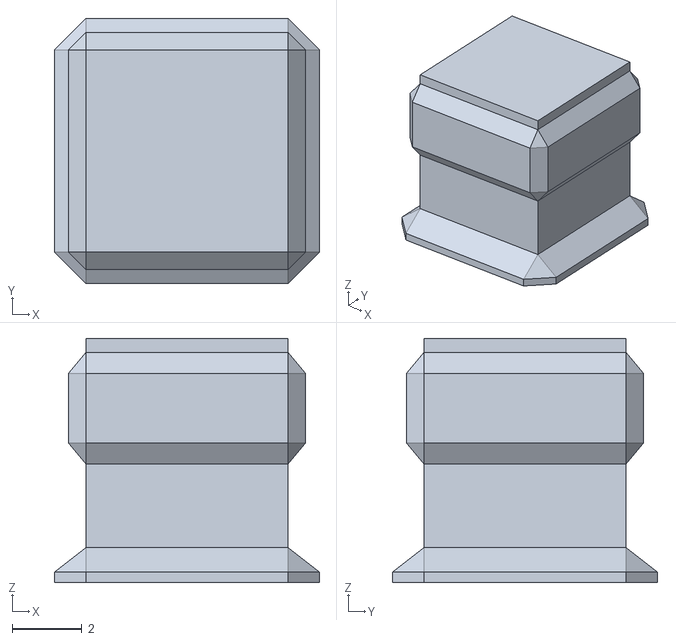
[picture p108: CAD file, 2022-04-12]
blender/clip-clip_hole_cad_export.stl
7.60 x 7.60 x 7.00
