WeirdConstructor/3DPrining_MakerGrid/blender/devices/led_strip_case-base.stl

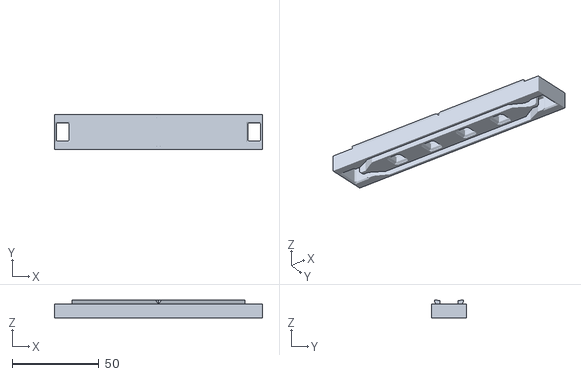
[picture p109: CAD file, 2022-01-31]
blender/devices/led_strip_case-base.stl
120.0 x 20.0 x 10.2
