WeirdConstructor/3DPrining_MakerGrid/blender/cases/raspberry_pi_plate-holder.stl

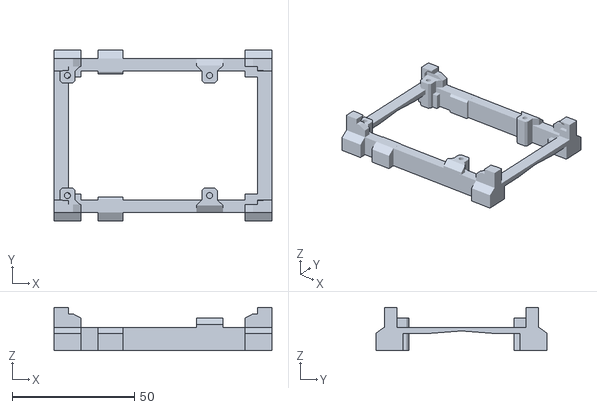
[picture p111: CAD file, 2022-01-18]
blender/cases/raspberry_pi_plate-holder.stl
89.0 x 70.0 x 17.6
