WeirdConstructor/3DPrining_MakerGrid/blender/clip-clip_holder_applied_trimmed_closed.stl

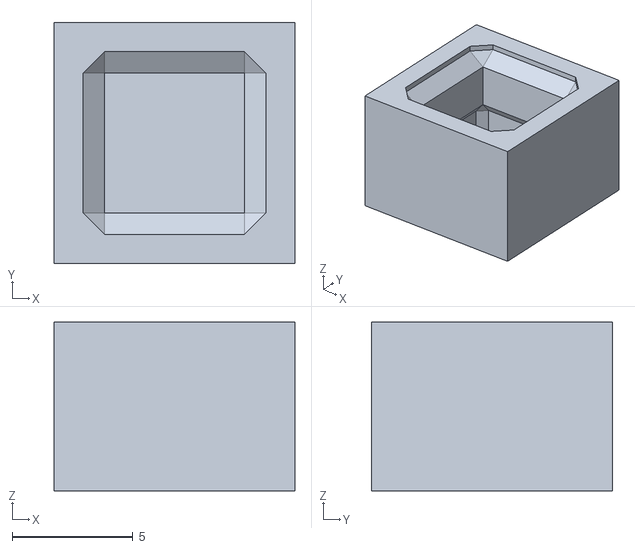
[picture p112: CAD file, 2022-04-12]
blender/clip-clip_holder_applied_trimmed_closed.stl
10.0 x 10.0 x 7.00
