WeirdConstructor/3DPrining_MakerGrid/blender/clip-clip_holder_negative_applied_trimmed.stl

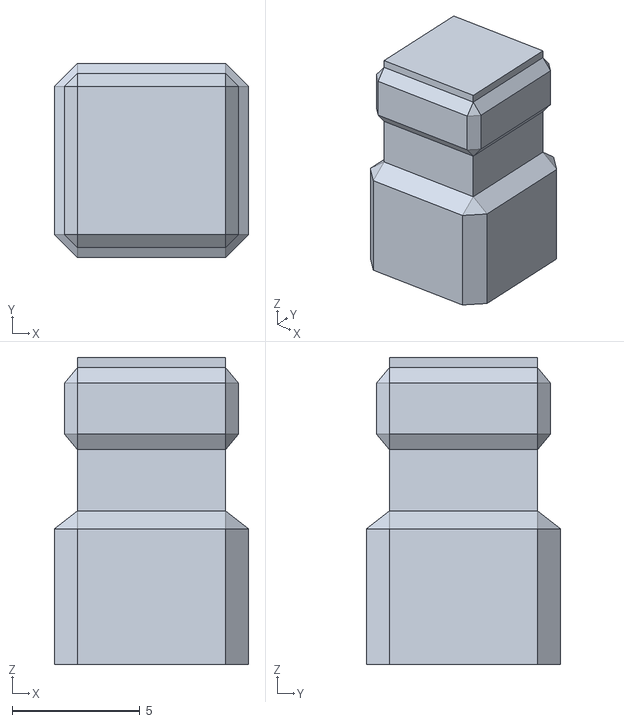
[picture p113: CAD file, 2022-04-12]
blender/clip-clip_holder_negative_applied_trimmed.stl
7.60 x 7.60 x 12.0
