WeirdConstructor/3DPrining_MakerGrid/blender/utils/plant_guide-hydro_bottom.stl

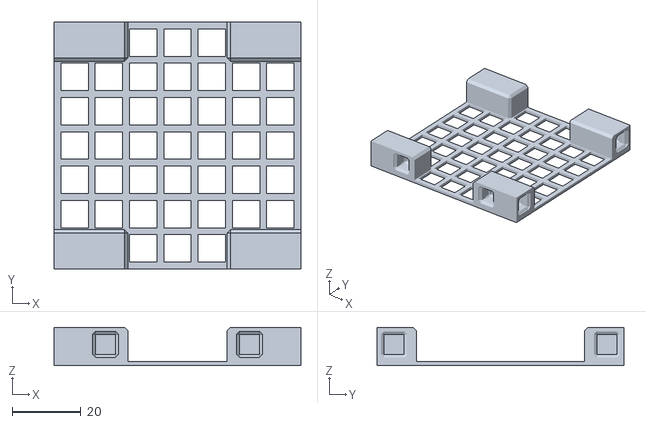
[picture p114: CAD file, 2024-06-11]
blender/utils/plant_guide-hydro_bottom.stl
72.0 x 72.0 x 11.2
