WeirdConstructor/3DPrining_MakerGrid/blender/cases/raspberry_pico_case_mkg_holder_v2.stl

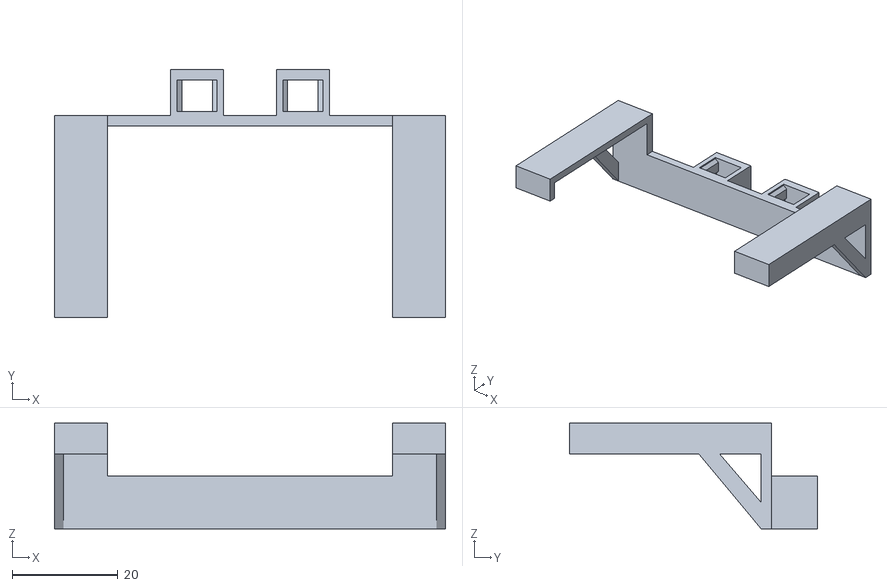
[picture p115: CAD file, 2022-01-14]
blender/cases/raspberry_pico_case_mkg_holder_v2.stl
74.0 x 47.0 x 20.0
