WeirdConstructor/3DPrining_MakerGrid/blender/clip-clip_holder_minimal.stl

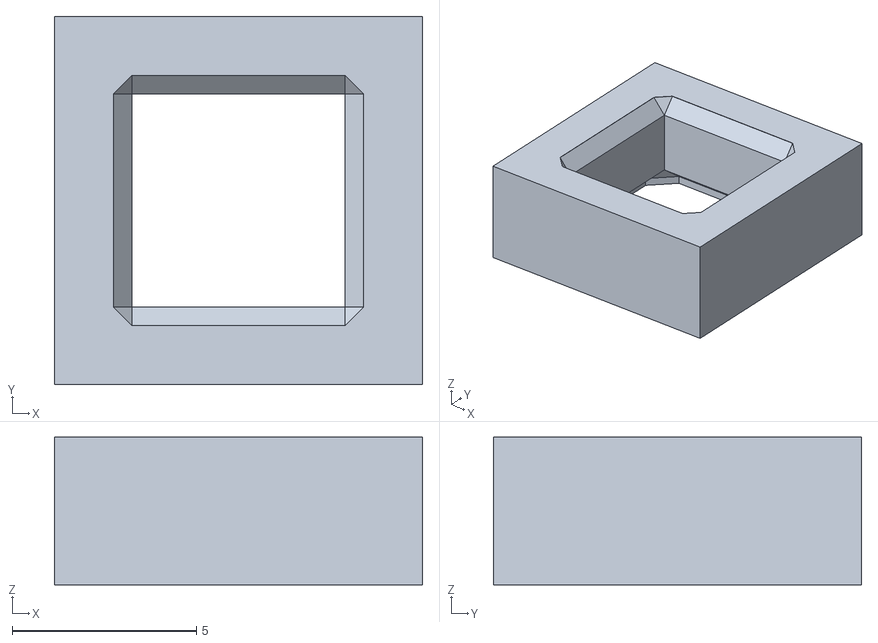
[picture p116: CAD file, 2022-04-12]
blender/clip-clip_holder_minimal.stl
10.0 x 10.0 x 4.01
