WeirdConstructor/3DPrining_MakerGrid/blender/utils/build_cubes-cube_corner_con_a_11x1.stl

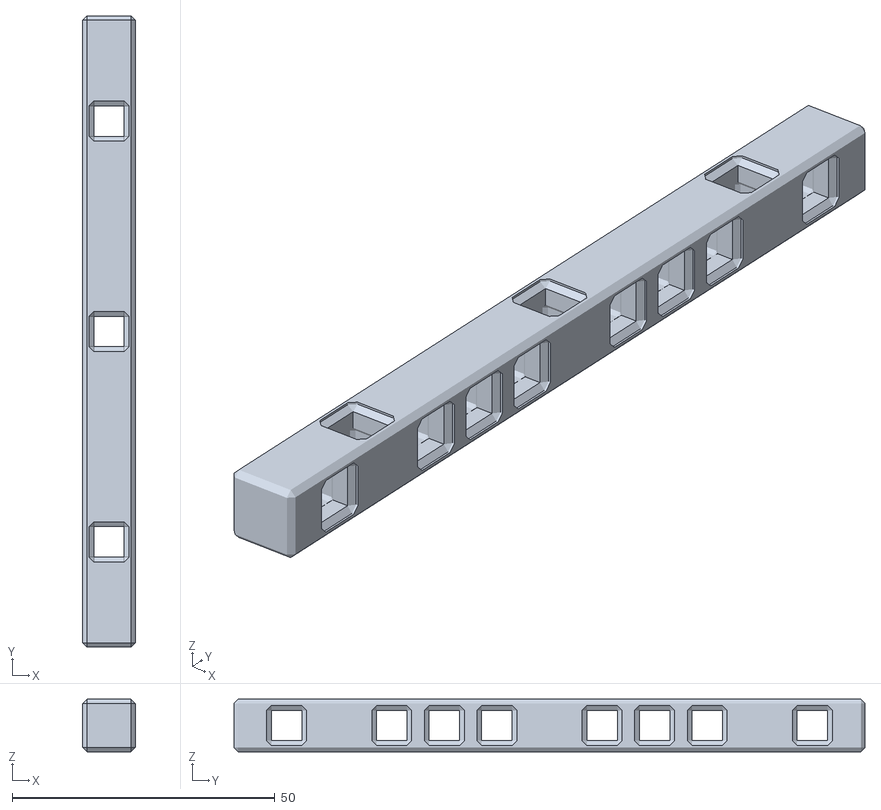
[picture p117: CAD file, 2024-04-21]
blender/utils/build_cubes-cube_corner_con_a_11x1.stl
10.0 x 120.0 x 10.0
