WeirdConstructor/3DPrining_MakerGrid/blender/clip-pole.stl

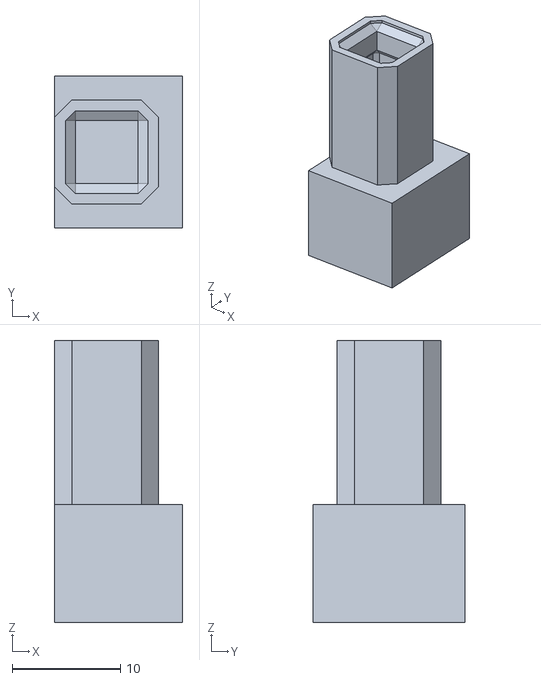
[picture p118: CAD file, 2022-02-16]
blender/clip-pole.stl
11.8 x 14.0 x 26.0
