WeirdConstructor/3DPrining_MakerGrid/blender/utils/build_cubes-cube_corner_con_a_7x1.stl

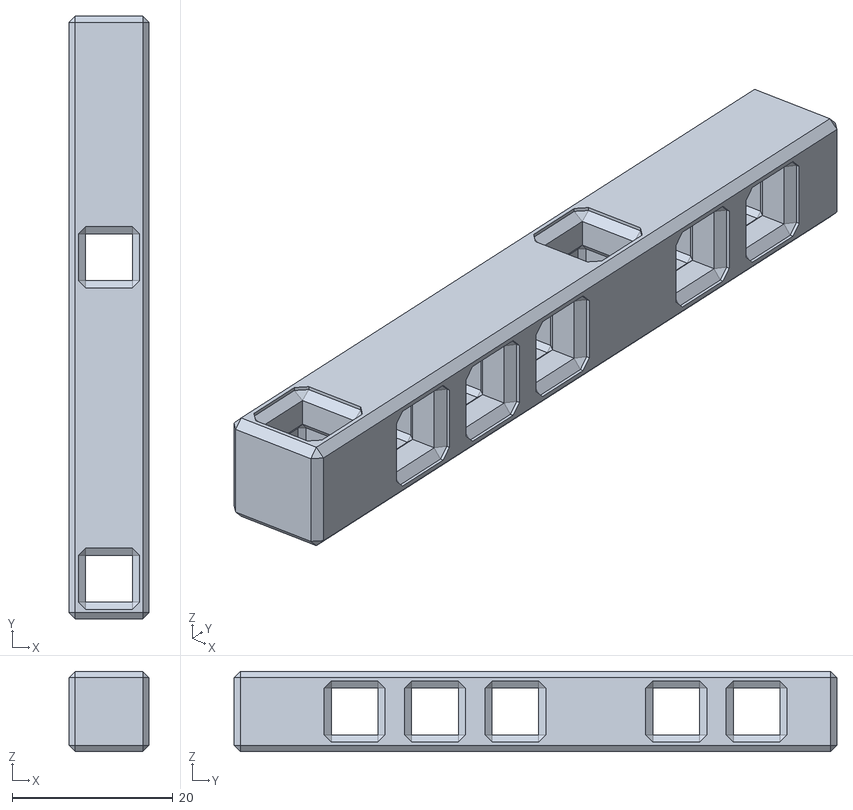
[picture p119: CAD file, 2024-04-21]
blender/utils/build_cubes-cube_corner_con_a_7x1.stl
10.0 x 75.0 x 10.0
