WeirdConstructor/3DPrining_MakerGrid/blender/clip-pole_holder.stl

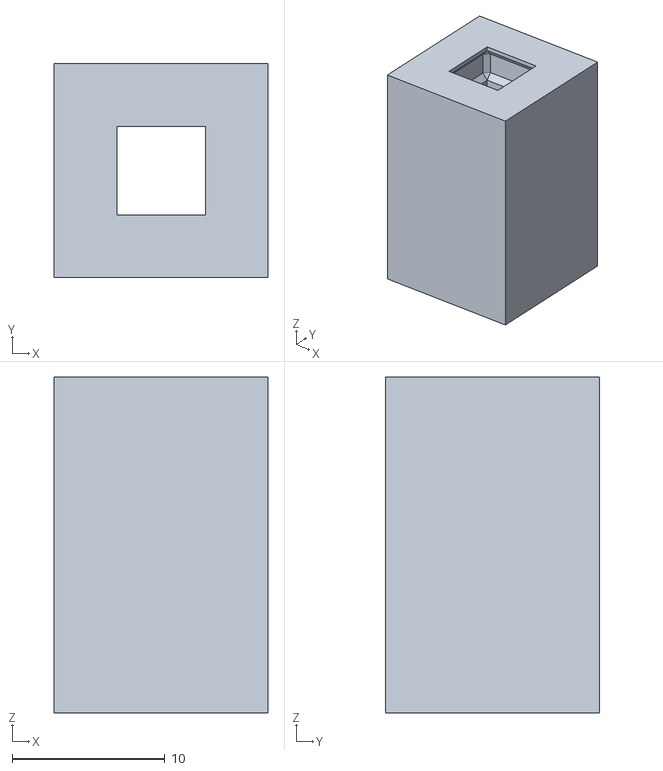
[picture p120: CAD file, 2022-02-13]
blender/clip-pole_holder.stl
14.0 x 14.0 x 22.0
