WeirdConstructor/3DPrining_MakerGrid/blender/utils/build_cubes-cube_corner_con_a_9x1.stl

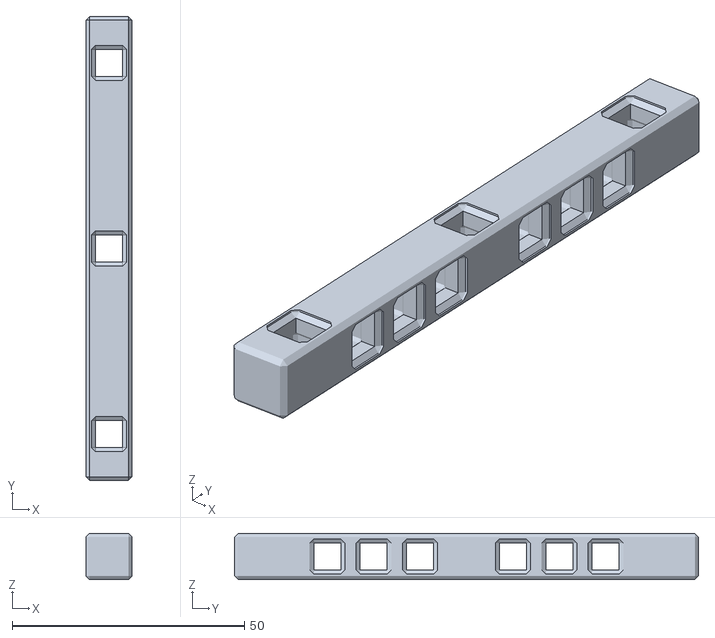
[picture p122: CAD file, 2024-04-21]
blender/utils/build_cubes-cube_corner_con_a_9x1.stl
10.0 x 100.0 x 10.0
