WeirdConstructor/3DPrining_MakerGrid/blender/clip-mini_clip.stl

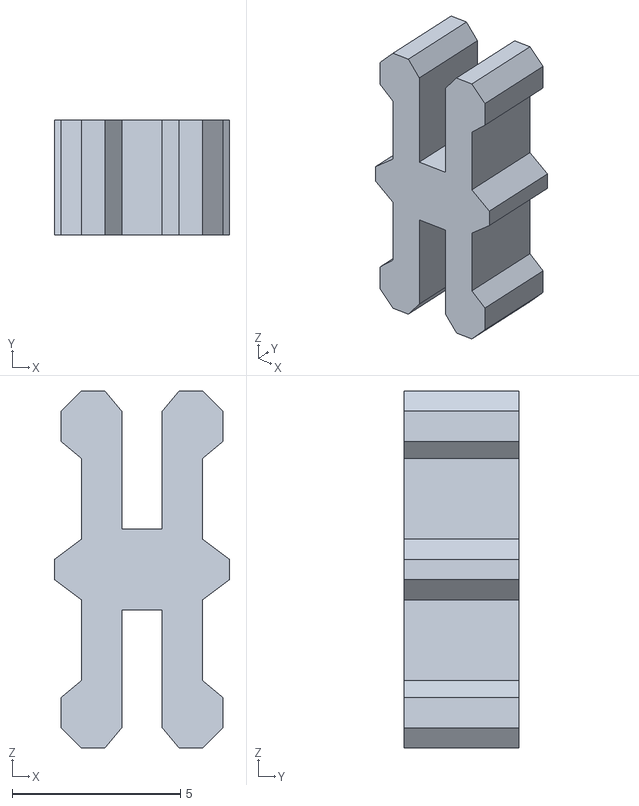
[picture p123: CAD file, 2022-01-18]
blender/clip-mini_clip.stl
5.20 x 3.40 x 10.6
