WeirdConstructor/3DPrining_MakerGrid/blender/utils/m4_dovetail_mount-side_clip.stl

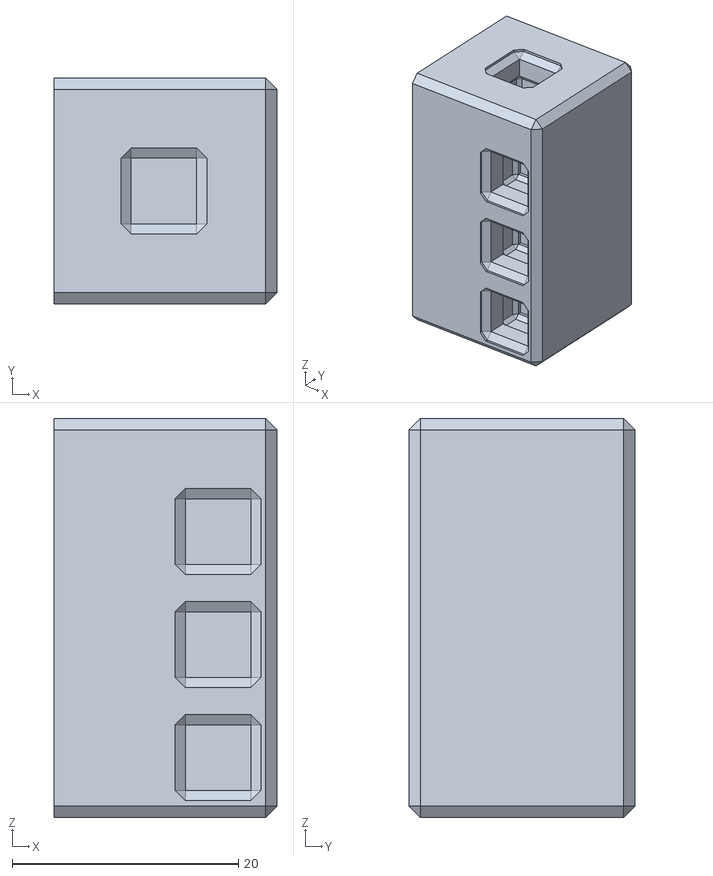
[picture p124: CAD file, 2024-03-30]
blender/utils/m4_dovetail_mount-side_clip.stl
19.7 x 20.0 x 35.3
