WeirdConstructor/3DPrining_MakerGrid/blender/clip-clip.stl

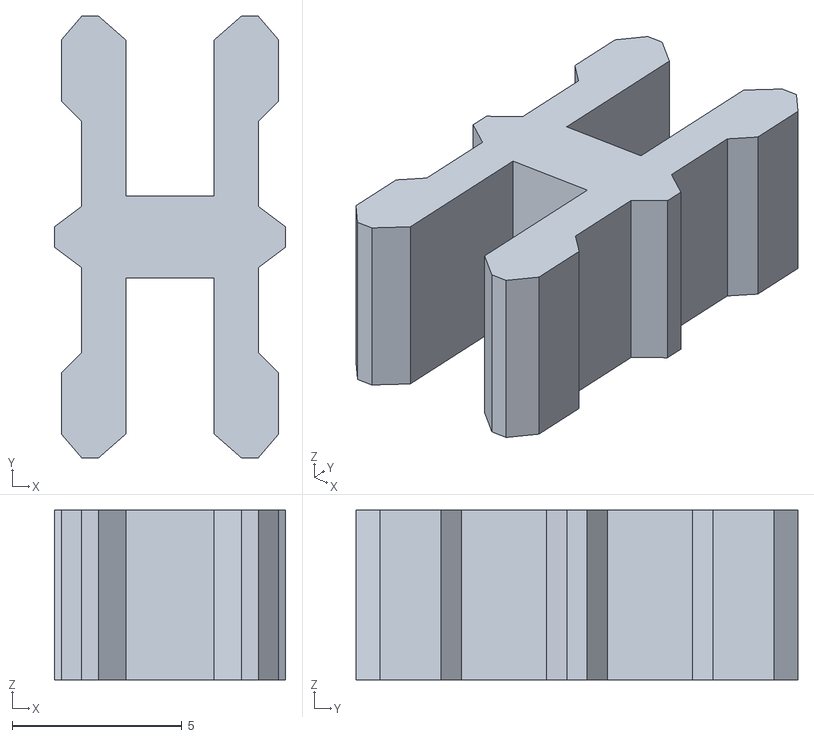
[picture p125: CAD file, 2022-01-18]
blender/clip-clip.stl
6.80 x 13.0 x 5.00
