WeirdConstructor/3DPrining_MakerGrid/blender/clip-mini_clip_holder.stl

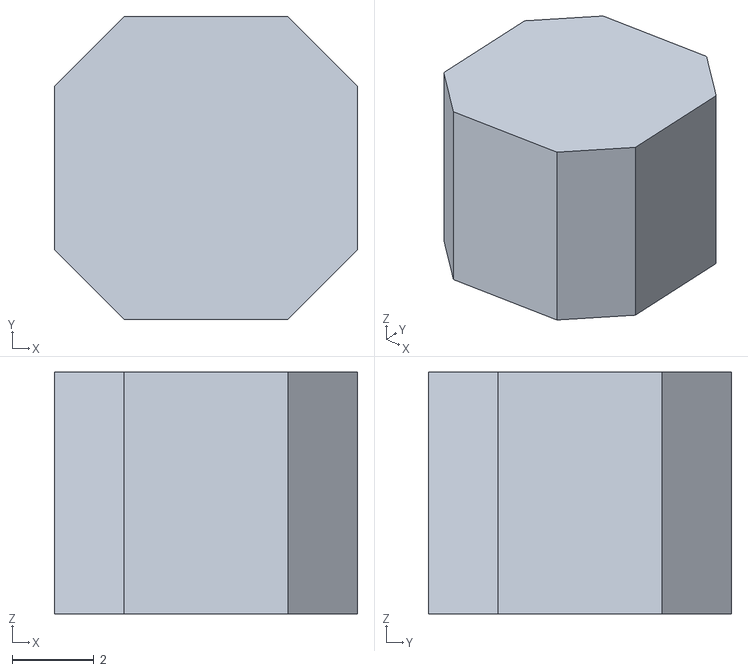
[picture p127: CAD file, 2022-01-18]
blender/clip-mini_clip_holder.stl
7.40 x 7.40 x 5.90
