WeirdConstructor/3DPrining_MakerGrid/blender/utils/container-10x8x3.stl

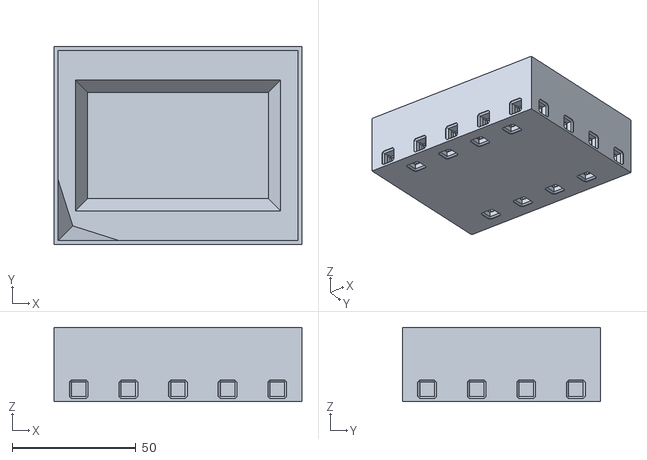
[picture p128: CAD file, 2022-05-31]
blender/utils/container-10x8x3.stl
100.0 x 80.0 x 30.0
