WeirdConstructor/3DPrining_MakerGrid/blender/utils/container-16x8x3.stl

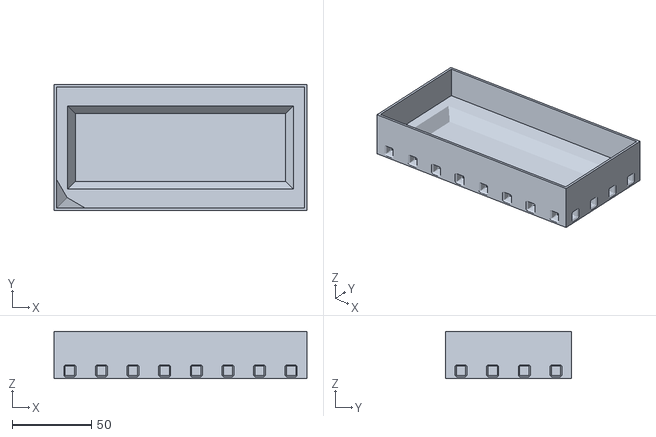
[picture p130: CAD file, 2022-05-31]
blender/utils/container-16x8x3.stl
160.0 x 80.0 x 30.0
