WeirdConstructor/3DPrining_MakerGrid/blender/utils/container-6x6x3.stl

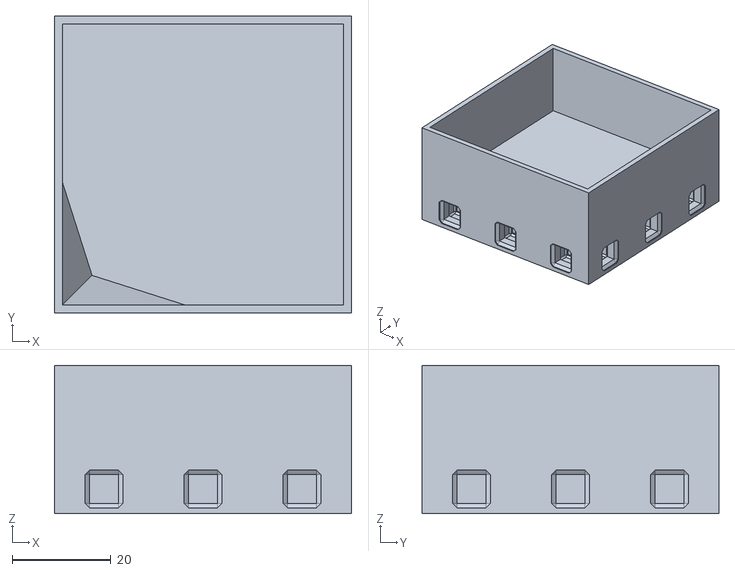
[picture p131: CAD file, 2022-05-31]
blender/utils/container-6x6x3.stl
60.0 x 60.0 x 30.0
