WeirdConstructor/3DPrining_MakerGrid/blender/utils/container-12x6x5.stl

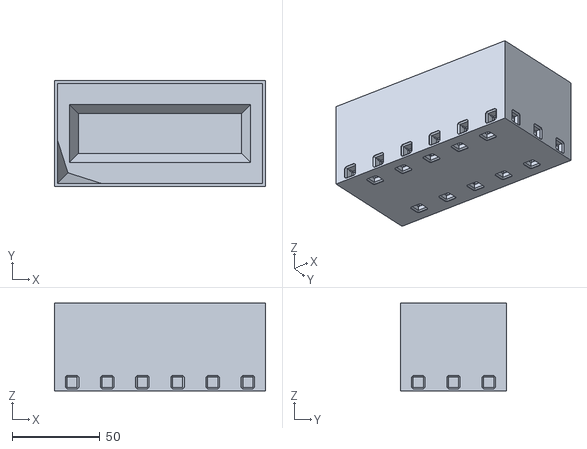
[picture p132: CAD file, 2022-05-31]
blender/utils/container-12x6x5.stl
120.0 x 60.0 x 50.0
