WeirdConstructor/3DPrining_MakerGrid/blender/clip_hole.stl

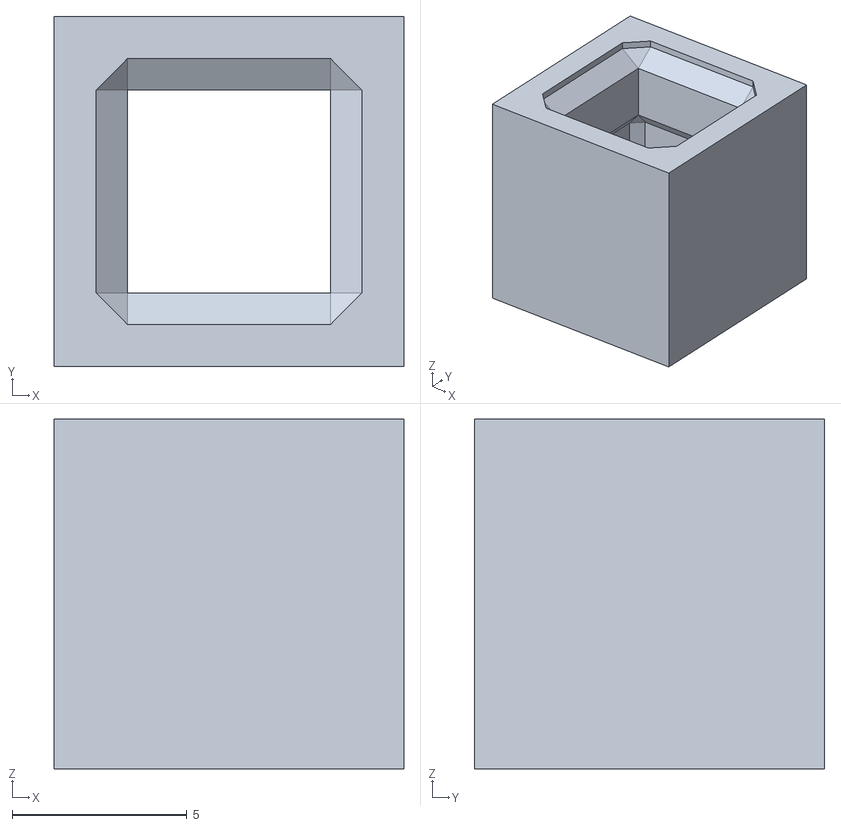
[picture p133: CAD file, 2022-01-15]
blender/clip_hole.stl
10.0 x 10.0 x 10.0
