WeirdConstructor/3DPrining_MakerGrid/blender/utils/container-14x12x5.stl

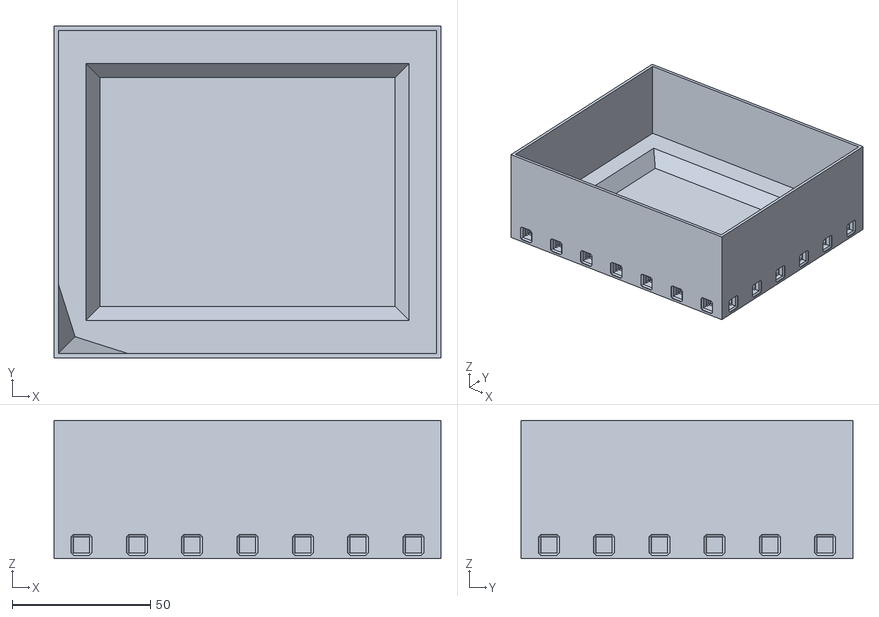
[picture p134: CAD file, 2022-05-31]
blender/utils/container-14x12x5.stl
140.0 x 120.0 x 50.0
