WeirdConstructor/3DPrining_MakerGrid/blender/utils/container-4x2x3.stl

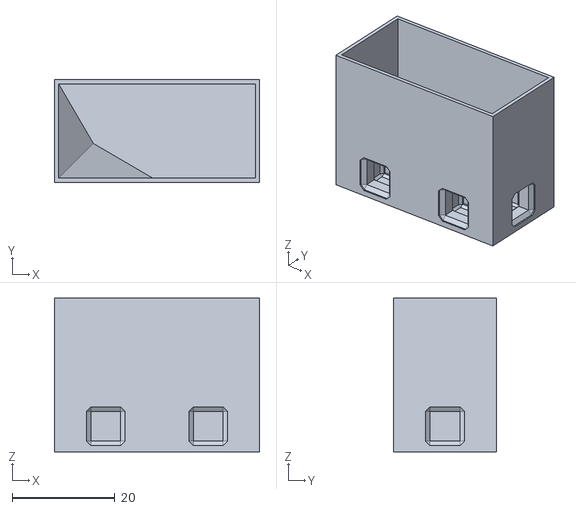
[picture p135: CAD file, 2022-05-31]
blender/utils/container-4x2x3.stl
40.0 x 20.0 x 30.0
