WeirdConstructor/3DPrining_MakerGrid/blender/utils/container-8x8x5.stl

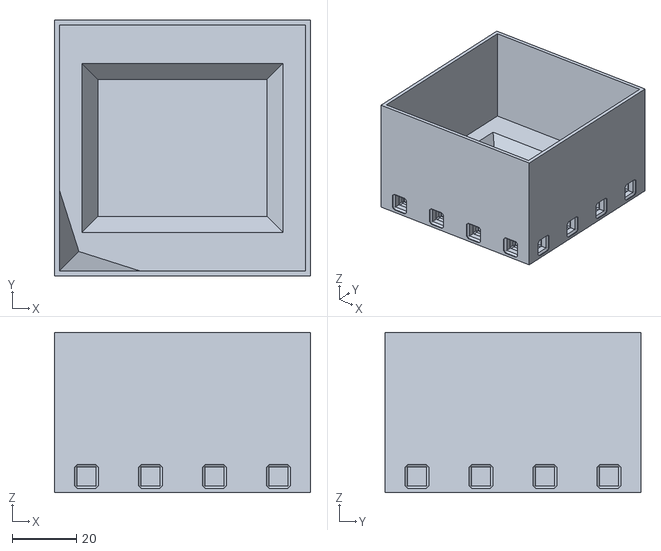
[picture p138: CAD file, 2022-05-31]
blender/utils/container-8x8x5.stl
80.0 x 80.0 x 50.0
