WeirdConstructor/3DPrining_MakerGrid/blender/utils/container-4x2x5.stl

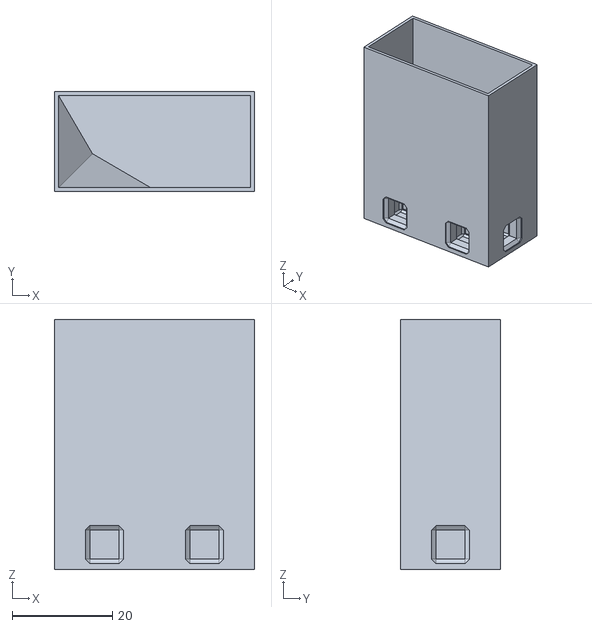
[picture p141: CAD file, 2022-05-31]
blender/utils/container-4x2x5.stl
40.0 x 20.0 x 50.0
