WeirdConstructor/3DPrining_MakerGrid/blender/utils/container-10x6x5.stl

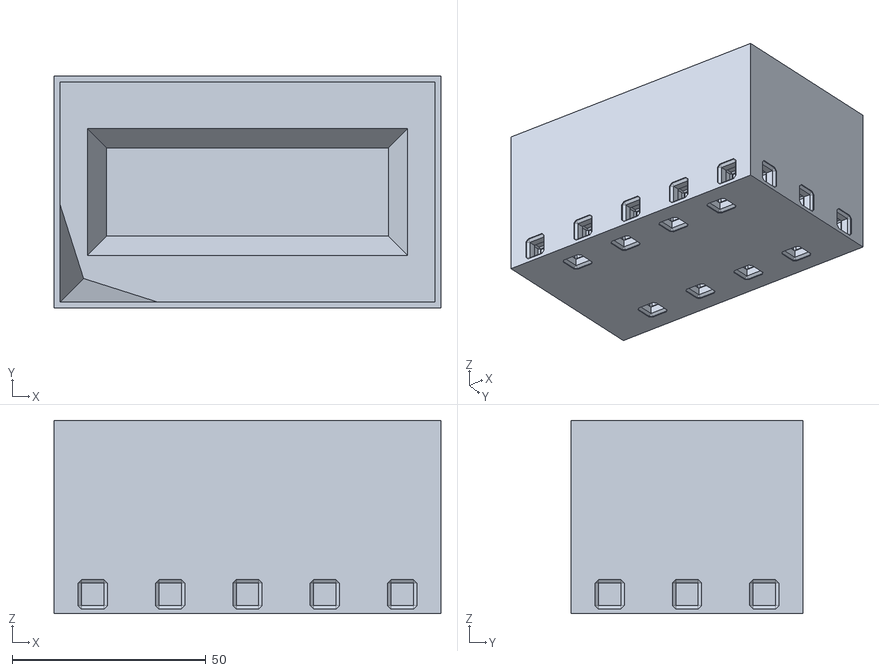
[picture p143: CAD file, 2022-05-31]
blender/utils/container-10x6x5.stl
100.0 x 60.0 x 50.0
