WeirdConstructor/3DPrining_MakerGrid/blender/utils/container-14x12x3.stl

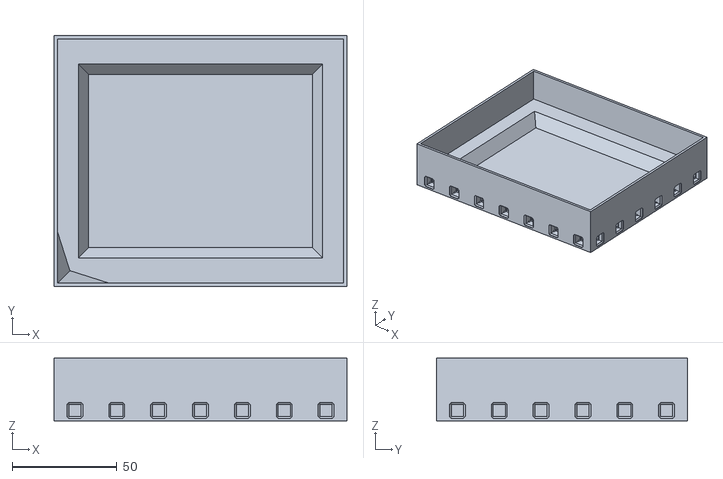
[picture p144: CAD file, 2022-05-31]
blender/utils/container-14x12x3.stl
140.0 x 120.0 x 30.0
