WeirdConstructor/3DPrining_MakerGrid/blender/utils/container-10x6x3.stl

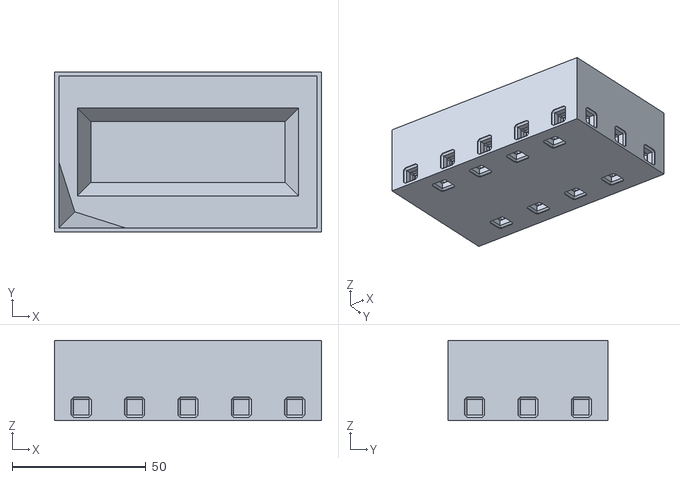
[picture p146: CAD file, 2022-05-31]
blender/utils/container-10x6x3.stl
100.0 x 60.0 x 30.0
