WeirdConstructor/3DPrining_MakerGrid/blender/utils/container-6x4x5.stl

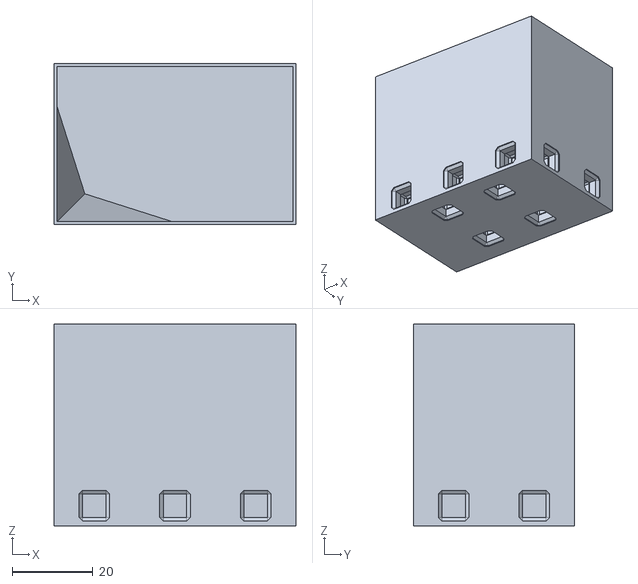
[picture p147: CAD file, 2022-05-31]
blender/utils/container-6x4x5.stl
60.0 x 40.0 x 50.0
