WeirdConstructor/3DPrining_MakerGrid/blender/utils/build_cubes-cube_two_con_3x1.stl

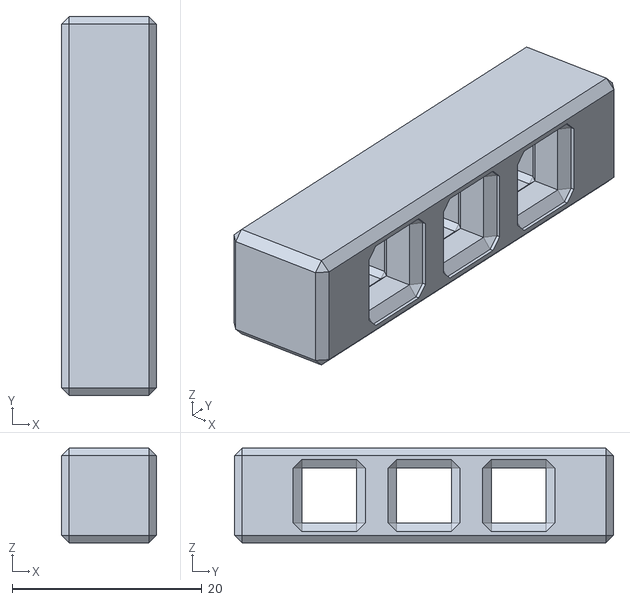
[picture p148: CAD file, 2022-05-07]
blender/utils/build_cubes-cube_two_con_3x1.stl
10.0 x 40.0 x 10.0
