WeirdConstructor/3DPrining_MakerGrid/blender/utils/build_cubes-cube_one_con_11x1.stl

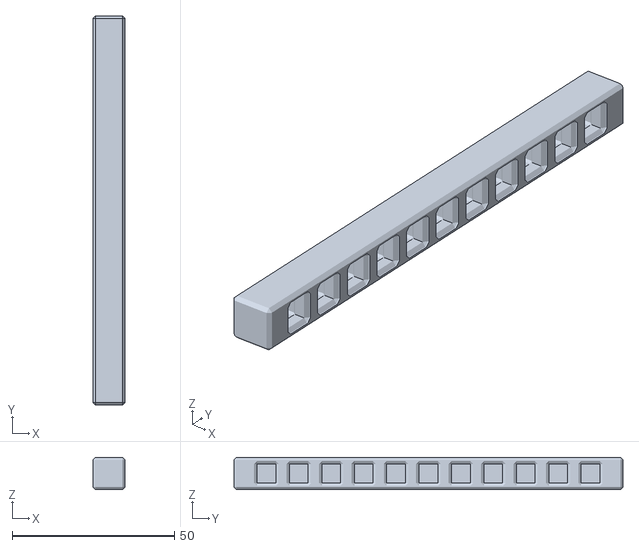
[picture p149: CAD file, 2022-05-07]
blender/utils/build_cubes-cube_one_con_11x1.stl
10.0 x 120.0 x 10.0
