WeirdConstructor/3DPrining_MakerGrid/blender/utils/build_cubes-cube_one_con_7x1.stl

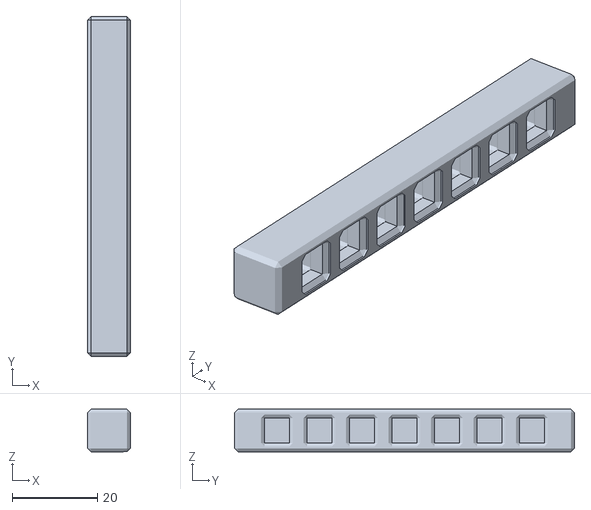
[picture p151: CAD file, 2022-05-07]
blender/utils/build_cubes-cube_one_con_7x1.stl
10.0 x 80.0 x 10.0
