WeirdConstructor/3DPrining_MakerGrid/blender/utils/build_cubes-cube_two_con_45deg_11x1.stl

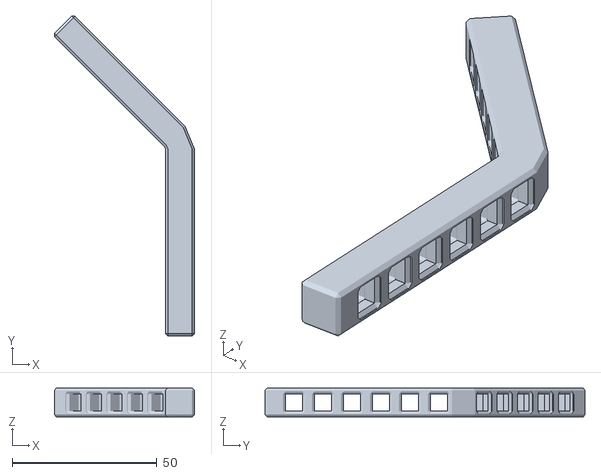
[picture p153: CAD file, 2022-05-07]
blender/utils/build_cubes-cube_two_con_45deg_11x1.stl
48.3 x 110.4 x 10.0
