WeirdConstructor/3DPrining_MakerGrid/blender/utils/cable_guide_type_c-holder_wide.stl

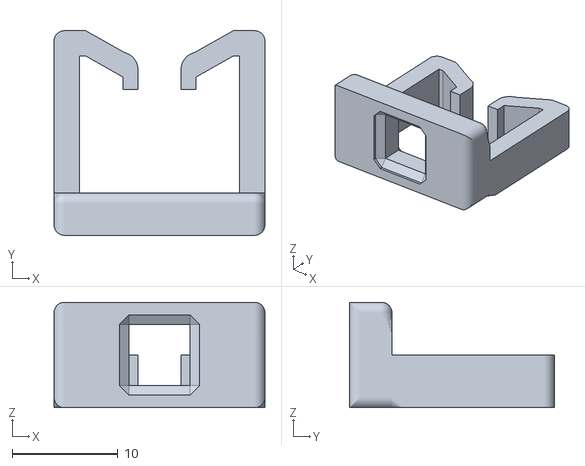
[picture p154: CAD file, 2022-05-06]
blender/utils/cable_guide_type_c-holder_wide.stl
20.0 x 19.4 x 10.0
