WeirdConstructor/3DPrining_MakerGrid/blender/utils/cable_guide_type_c-holder_medium.stl

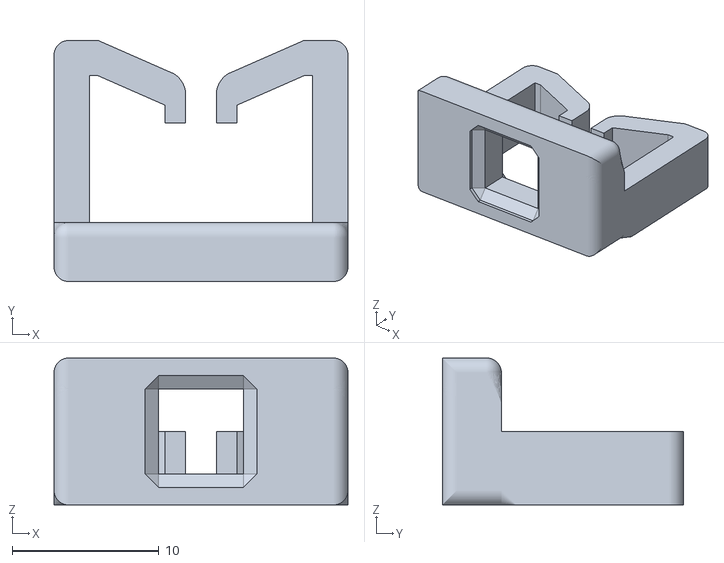
[picture p155: CAD file, 2022-05-06]
blender/utils/cable_guide_type_c-holder_medium.stl
20.0 x 16.4 x 10.0
