WeirdConstructor/3DPrining_MakerGrid/blender/utils/cable_guide_type_b-plate.stl

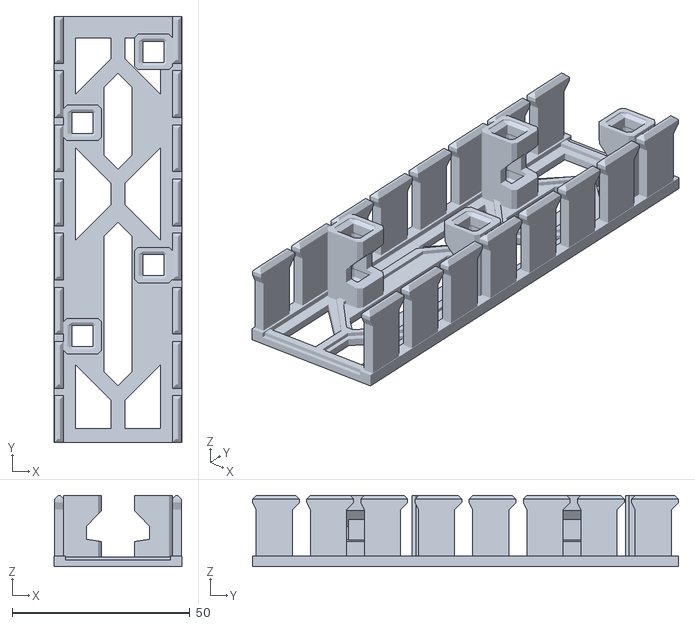
[picture p156: CAD file, 2022-05-06]
blender/utils/cable_guide_type_b-plate.stl
36.0 x 120.0 x 20.0
