WeirdConstructor/3DPrining_MakerGrid/blender/utils/cable_guide_type_c-holder_stacked.stl

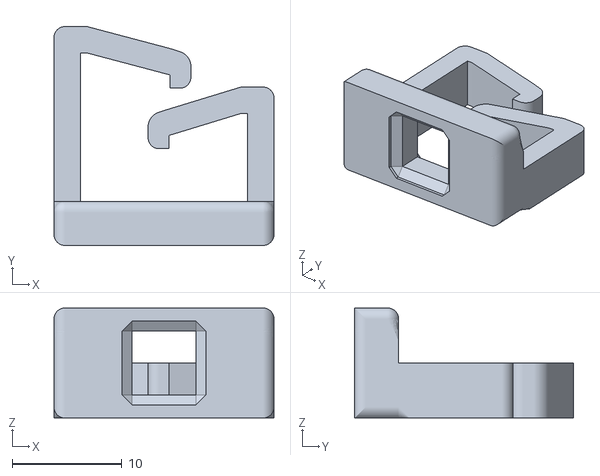
[picture p157: CAD file, 2022-05-06]
blender/utils/cable_guide_type_c-holder_stacked.stl
20.0 x 19.9 x 10.0
