WeirdConstructor/3DPrining_MakerGrid/blender/utils/fans-axial_12025_holder.stl

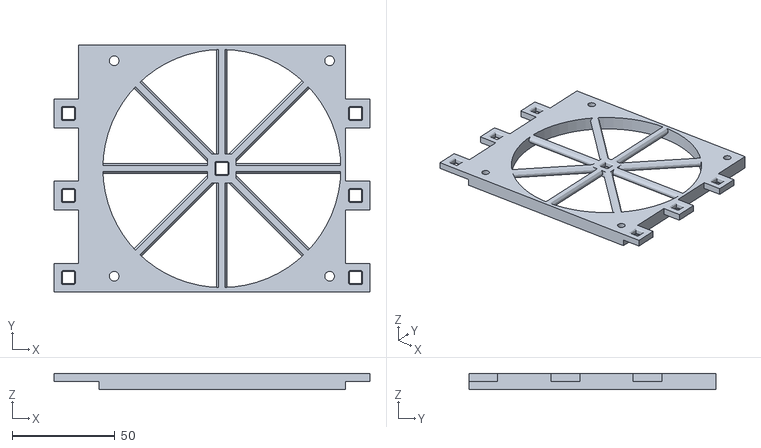
[picture p158: CAD file, 2022-05-05]
blender/utils/fans-axial_12025_holder.stl
154.0 x 120.4 x 8.01
