WeirdConstructor/3DPrining_MakerGrid/blender/utils/fans-axial_5015_holder.stl

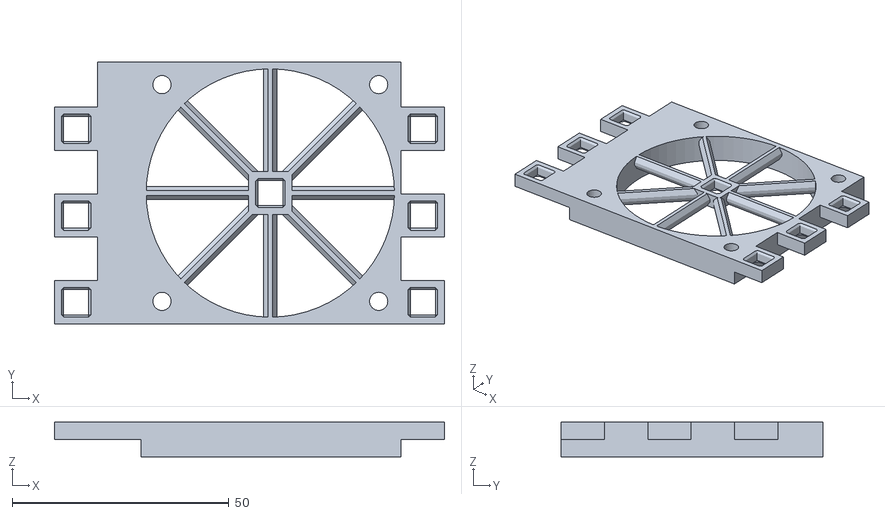
[picture p159: CAD file, 2022-05-05]
blender/utils/fans-axial_5015_holder.stl
90.0 x 60.4 x 8.01
