WeirdConstructor/3DPrining_MakerGrid/blender/utils/build_cubes-cube_3x1.stl

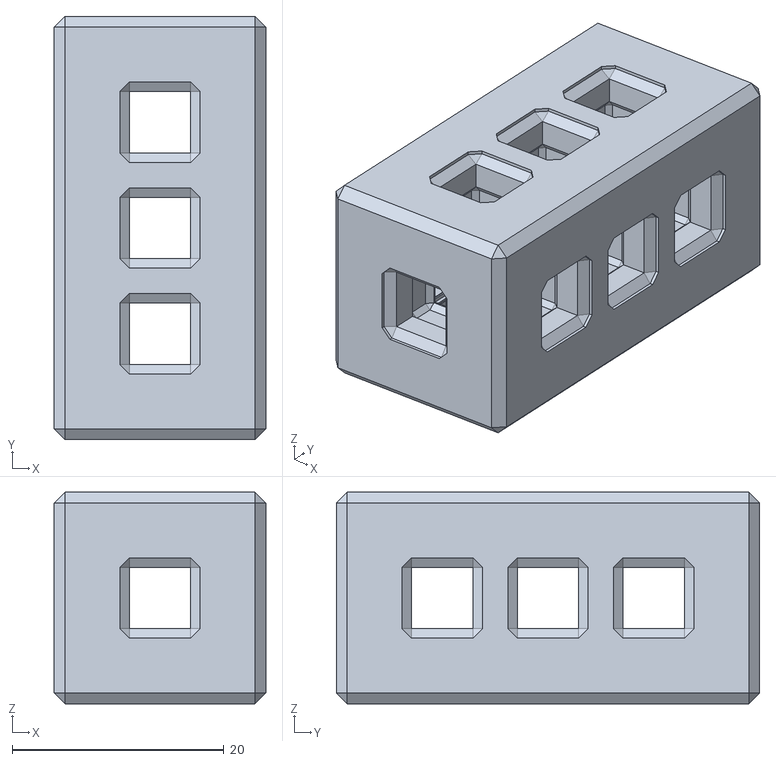
[picture p160: CAD file, 2022-05-05]
blender/utils/build_cubes-cube_3x1.stl
20.0 x 40.0 x 20.0
