WeirdConstructor/3DPrining_MakerGrid/blender/utils/cable_guide_type_c-holder_small.stl

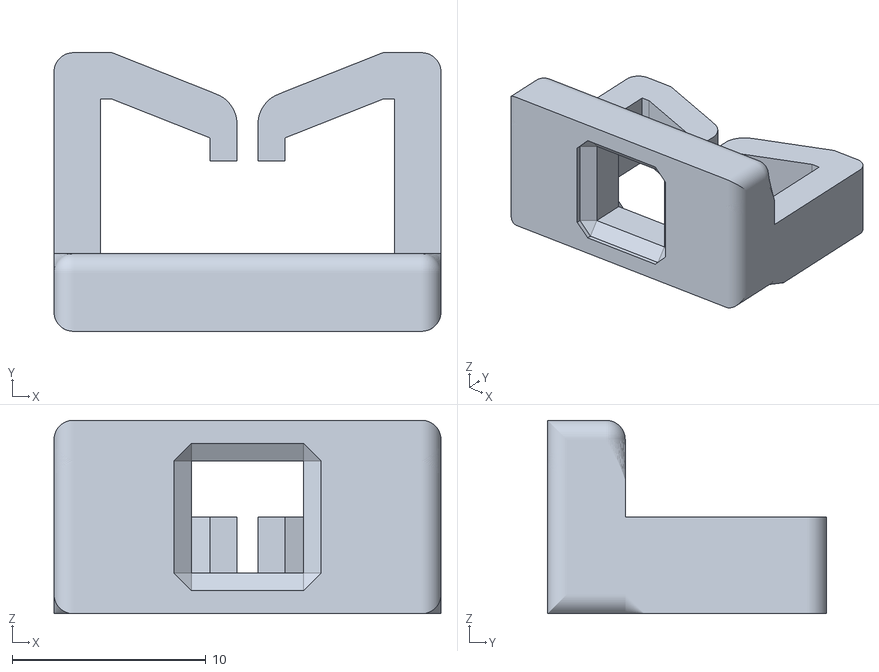
[picture p161: CAD file, 2022-04-18]
blender/utils/cable_guide_type_c-holder_small.stl
20.0 x 14.4 x 10.0
