WeirdConstructor/3DPrining_MakerGrid/blender/utils/t_slot_profile_util-m5_mount_with_align.stl

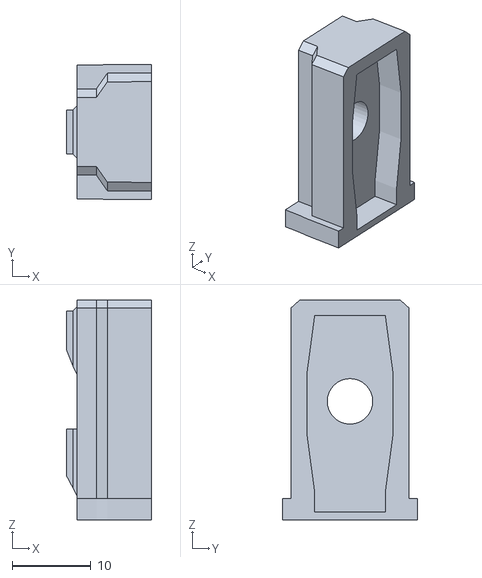
[picture p162: CAD file, 2022-04-18]
blender/utils/t_slot_profile_util-m5_mount_with_align.stl
10.8 x 17.2 x 28.0
