WeirdConstructor/3DPrining_MakerGrid/blender/utils/t_slot_profile_util-m5_mount.stl

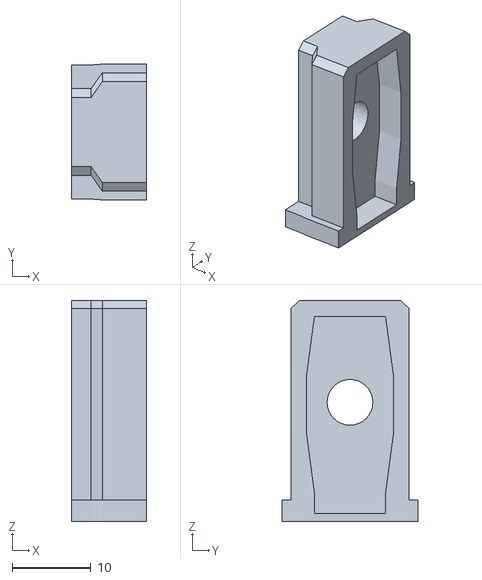
[picture p163: CAD file, 2022-03-28]
blender/utils/t_slot_profile_util-m5_mount.stl
9.50 x 17.2 x 28.0
