WeirdConstructor/3DPrining_MakerGrid/blender/utils/build_cubes-cube_11x1_x.stl

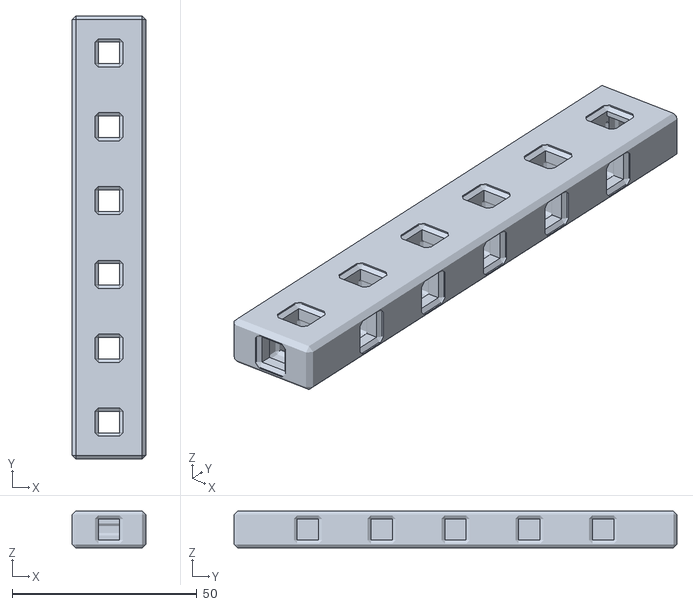
[picture p164: CAD file, 2022-03-17]
blender/utils/build_cubes-cube_11x1_x.stl
20.0 x 120.0 x 10.0
