WeirdConstructor/3DPrining_MakerGrid/blender/utils/cont_shelf-pole_160mm.stl

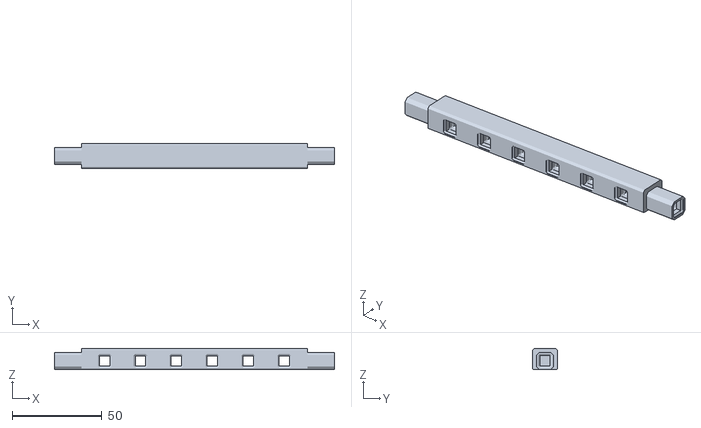
[picture p165: CAD file, 2022-02-22]
blender/utils/cont_shelf-pole_160mm.stl
156.0 x 14.0 x 11.8
