WeirdConstructor/3DPrining_MakerGrid/blender/utils/container-3x3x3.stl

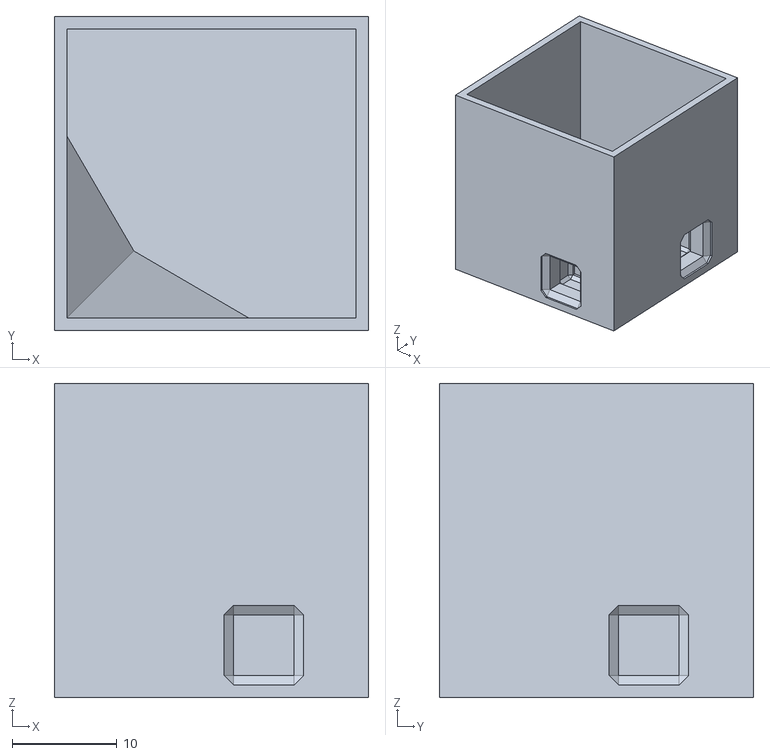
[picture p166: CAD file, 2022-02-22]
blender/utils/container-3x3x3.stl
30.0 x 30.0 x 30.0
