WeirdConstructor/3DPrining_MakerGrid/blender/utils/container-6x3x3.stl

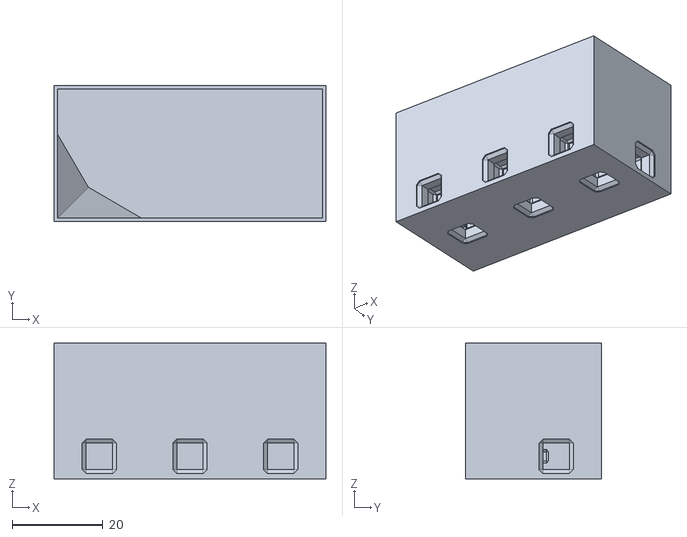
[picture p167: CAD file, 2022-02-22]
blender/utils/container-6x3x3.stl
60.0 x 30.0 x 30.0
