WeirdConstructor/3DPrining_MakerGrid/blender/utils/container-4x3x3.stl

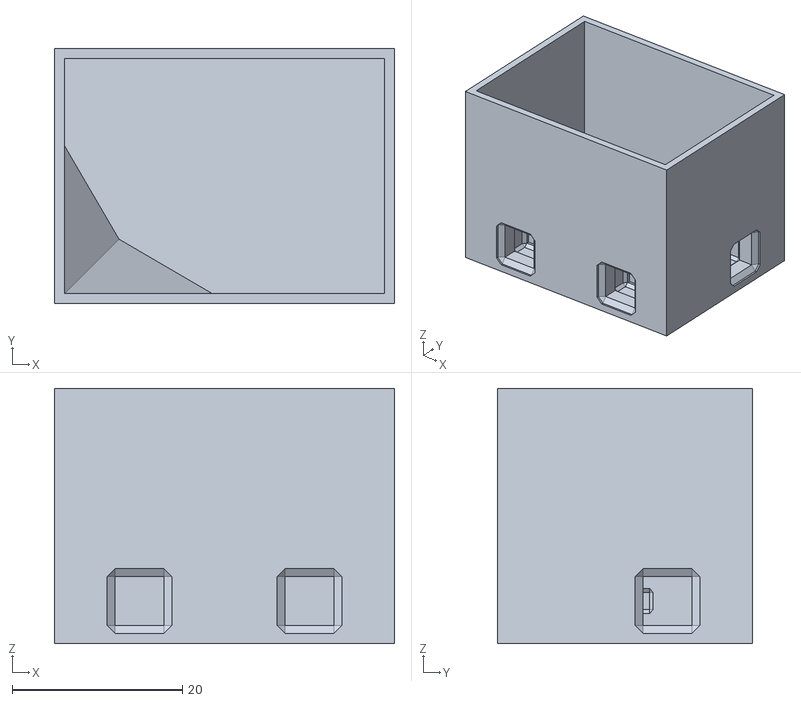
[picture p168: CAD file, 2022-02-22]
blender/utils/container-4x3x3.stl
40.0 x 30.0 x 30.0
