WeirdConstructor/3DPrining_MakerGrid/blender/utils/container-6x12x5.stl

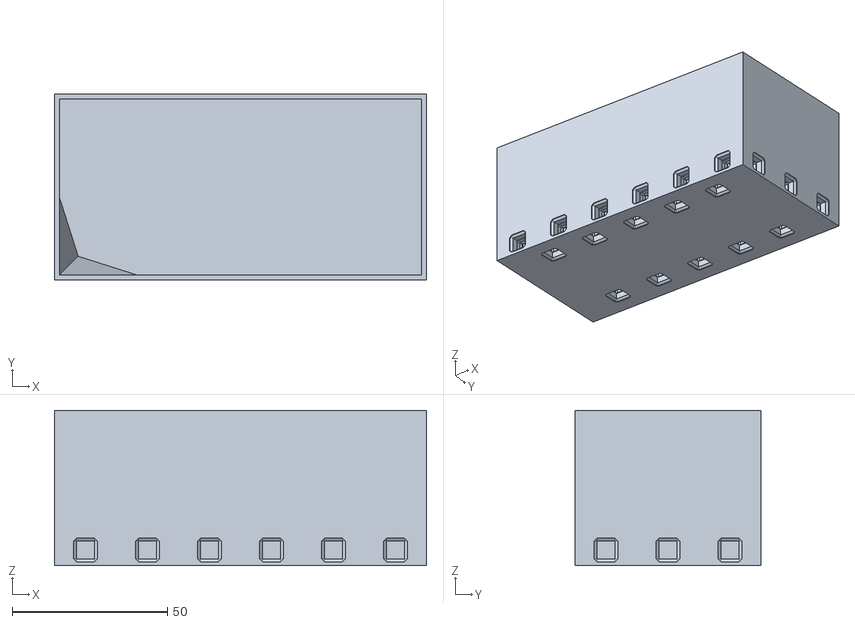
[picture p169: CAD file, 2022-02-22]
blender/utils/container-6x12x5.stl
120.0 x 60.0 x 50.0
